GustaEagle/TCC_Calculadora_Acessivel/cronograma/cronograma.md

# Cronograma do projeto (calculadora — TCC)

Documento de referência temporal: organização **semana a semana**, com base no consolidado que você já tinha (intervalos e marcos com data única).  
Não substitui PRD, casos de uso, requisitos nem demais artefatos de engenharia de software — serve só como **linha do tempo** para alinhar entregas físicas, texto do trabalho e material de apresentação.

---

## Como ler este cronograma

- **Semanas:** domingo a sábado, numeradas a partir de **01/03/2026** (domingo).
- **“Em vigência”:** intervalos do plano original que **cruzam** aquela semana (podem continuar nas semanas seguintes).
- **“Marcos (data única)”:** acontecimentos previstos para um dia específico no consolidado.
- **Última data do consolidado:** **25/09/2026** (término previsto da criação do banner). Ajuste o fechamento com a data real da banca ou do curso, se for anterior.

---

## Visão geral do horizonte

| Marco global | Data |
| --- | --- |
| Início do consolidado | 01/03/2026 |
| Última data registrada | 25/09/2026 |

---

## Datas importantes (equipe / instituição)

Estas datas **complementam** o export bruto em [`cronograma_raw.txt`](cronograma_raw.txt) e deixam explícitos compromissos já combinados com orientação.

| Data | Significado |
| ---- | --- |
| **24/05/2026** | **Parte escrita homologada** com o professor **Yuri**: introdução; materiais e métodos; resultados e discussão; **esboço** de conclusão (texto praticamente aceito nesse conjunto). |
| **10/06/2026** | **Entrega da parte física + software**: produto integrado (hardware encapsulado + software embarcado) alinhado ao marco de **encapsulamento finalizado** do plano. |

---

## Cronograma semanal

### Março de 2026

#### Semana 1 — 01/03 a 07/03/2026

**Em vigência:** fabricação do teclado; teste no monitor; encapsulamento; testes aritméticos.

#### Semana 2 — 08/03 a 14/03/2026

**Em vigência:** fabricação do teclado; teste no monitor; encapsulamento; testes aritméticos.

#### Semana 3 — 15/03 a 21/03/2026

**Em vigência:** fabricação do teclado; teste no monitor; encapsulamento; testes aritméticos; agendamento de reunião (até 01/04/2026).

#### Semana 4 — 22/03 a 28/03/2026

**Em vigência:** fabricação do teclado; teste no monitor; encapsulamento; testes aritméticos; agendamento de reunião (até 01/04/2026).

#### Semana 5 — 29/03 a 04/04/2026

**Em vigência:** fabricação do teclado; teste no monitor; encapsulamento; testes aritméticos; agendamento de reunião (até 01/04/2026).

---

### Abril de 2026

#### Semana 6 — 05/04 a 11/04/2026

**Em vigência:** fabricação do teclado; teste no monitor; encapsulamento; testes aritméticos; **materiais e métodos (texto do TCC, 02/04 a 21/04)**; resultados e discussões (texto do TCC, a partir de 10/04).

#### Semana 7 — 12/04 a 18/04/2026

**Em vigência:** fabricação do teclado; teste no monitor; encapsulamento; testes aritméticos; **materiais e métodos (texto do TCC, até 21/04)**; resultados e discussões (texto do TCC); introdução (texto do TCC, a partir de 13/04).

#### Semana 8 — 19/04 a 25/04/2026

**Em vigência:** fabricação do teclado; encapsulamento; testes aritméticos; **materiais e métodos (texto do TCC, até 21/04)**; resultados e discussões (texto do TCC); introdução (texto do TCC); desenvolvimento (texto do TCC, a partir de 23/04).  
**Observação:** o intervalo de **teste no monitor** encerra em **15/04/2026** (semana anterior), logo ele não aparece mais a partir desta semana.  
**Marcos (export bruto):** fabricação PCB **07/04**; teste de PCB **14/04**; partes visuais **15/04**; revisão documentação **20/04**; refabricação e ajustes **24/04**; aquisição da bateria **25/04** (ver tabela de referência).

#### Semana 9 — 26/04 a 02/05/2026

**Em vigência:** fabricação do teclado; encapsulamento; testes aritméticos; resultados e discussões (texto do TCC); introdução (texto do TCC); desenvolvimento (texto do TCC).  
**Marcos (data única):** testes PCB 02 em **01/05/2026**.

---

### Maio de 2026

#### Semana 10 — 03/05 a 09/05/2026

**Em vigência:** encapsulamento; testes aritméticos; resultados e discussões (texto do TCC); introdução (texto do TCC); desenvolvimento (texto do TCC); resultados (texto do TCC, a partir de 05/05).  
**Marcos (data única):** revisão introdução (professor) em **04/05/2026**.

#### Semana 11 — 10/05 a 16/05/2026

**Em vigência:** encapsulamento; resultados e discussões (texto do TCC); desenvolvimento (texto do TCC); resultados (texto do TCC); conclusão (texto do TCC, a partir de 15/05); criação de banner (a partir de 15/05).  
**Marcos (data única):** revisão de documentação em **10/05/2026**; revisão materiais e métodos em **14/05/2026**; testes logarítmicos em **15/05/2026**.

#### Semana 12 — 17/05 a 23/05/2026

**Em vigência:** encapsulamento; resultados e discussões (texto do TCC); resultados (texto do TCC); conclusão (texto do TCC); criação de banner.  
**Marcos (data única):** revisão resultados e discussão (professor) em **18/05/2026**; outras funções (testes) em **22/05/2026**; revisão conclusão e revisão final em **23/05/2026**.

#### Semana 13 — 24/05 a 30/05/2026

**Em vigência:** encapsulamento; conclusão (texto do TCC); criação de banner.  
**Marcos (equipe):** **24/05/2026** — parte escrita homologada com o **prof. Yuri** (introdução; materiais e métodos; resultados e discussão; esboço de conclusão). Ver secção [Datas importantes](#datas-importantes-equipe--instituição).

---

### Junho de 2026

#### Semana 14 — 31/05 a 06/06/2026

**Em vigência:** encapsulamento; criação de banner.

#### Semana 15 — 07/06 a 13/06/2026

**Em vigência:** encapsulamento; criação de banner.  
**Marcos (data única):** **10/06/2026** — **encapsulamento finalizado** no consolidado; na prática da equipe, **entrega da parte física + software** (produto integrado). Ver secção [Datas importantes](#datas-importantes-equipe--instituição).

#### Semana 16 — 14/06 a 20/06/2026

**Em vigência:** criação de banner (até **25/09/2026**).

---

### Julho a setembro de 2026

Do **21/06/2026** em diante, o consolidado não traz novos intervalos além da **criação de banner**, com término previsto em **25/09/2026**. As semanas abaixo documentam esse período de forma explícita, sem inventar entregas intermediárias.

#### Semana 17 — 21/06 a 27/06/2026

**Em vigência:** criação de banner (até 25/09/2026).

#### Semana 18 — 28/06 a 04/07/2026

**Em vigência:** criação de banner (até 25/09/2026).

#### Semana 19 — 05/07 a 11/07/2026

**Em vigência:** criação de banner (até 25/09/2026).

#### Semana 20 — 12/07 a 18/07/2026

**Em vigência:** criação de banner (até 25/09/2026).

#### Semana 21 — 19/07 a 25/07/2026

**Em vigência:** criação de banner (até 25/09/2026).

#### Semana 22 — 26/07 a 01/08/2026

**Em vigência:** criação de banner (até 25/09/2026).

#### Semana 23 — 02/08 a 08/08/2026

**Em vigência:** criação de banner (até 25/09/2026).

#### Semana 24 — 09/08 a 15/08/2026

**Em vigência:** criação de banner (até 25/09/2026).

#### Semana 25 — 16/08 a 22/08/2026

**Em vigência:** criação de banner (até 25/09/2026).

#### Semana 26 — 23/08 a 29/08/2026

**Em vigência:** criação de banner (até 25/09/2026).

#### Semana 27 — 30/08 a 05/09/2026

**Em vigência:** criação de banner (até 25/09/2026).

#### Semana 28 — 06/09 a 12/09/2026

**Em vigência:** criação de banner (até 25/09/2026).

#### Semana 29 — 13/09 a 19/09/2026

**Em vigência:** criação de banner (até 25/09/2026).

#### Semana 30 — 20/09 a 26/09/2026

**Em vigência:** criação de banner (até **25/09/2026** — último dia previsto no consolidado).

---

## Referência: intervalos e datas do consolidado original

Tabela de conferência alinhada ao export [`cronograma_raw.txt`](cronograma_raw.txt) (Google Calendar), mais as **datas importantes** da equipe.  
_Notas:_ no raw aparece um evento “Encapsulamento finalizado” em **25/04** junto de “Aquisição da bateria”; isso **conflita** com o intervalo de encapsulamento até **10/06**. Aqui mantém-se **10/06** como encerramento do encapsulamento; **25/04** figura só como aquisição da bateria.

| Período / data | Descrição |
| --- | --- |
| 01/03/2026 a 01/05/2026 | Fabricação do teclado |
| 01/03/2026 a 15/04/2026 | Teste no monitor |
| 01/03/2026 a 10/06/2026 | Encapsulamento |
| 01/03/2026 a 04/05/2026 | Testes aritméticos |
| 18/03/2026 a 01/04/2026 | Agendar reunião |
| 02/04/2026 a 21/04/2026 | Materiais e métodos (texto TCC) |
| 10/04/2026 a 18/05/2026 | Resultados e discussões (texto TCC) |
| 13/04/2026 a 03/05/2026 | Introdução (texto TCC) |
| 23/04/2026 a 13/05/2026 | Desenvolvimento (texto TCC) |
| 05/05/2026 a 22/05/2026 | Resultados (texto TCC) |
| 15/05/2026 a 30/05/2026 | Conclusão (texto TCC) |
| 15/05/2026 a 25/09/2026 | Criação de banner |
| 02/04/2026 | Revisão documentação (dia inteiro) |
| 07/04/2026 | Fabricação PCB |
| 10/04/2026 | Revisão documentação; início resultados e discussões (texto) |
| 14/04/2026 | Teste de PCB |
| 15/04/2026 | Partes visuais |
| 20/04/2026 | Revisão documentação |
| 24/04/2026 | Refabricação e ajustes |
| 25/04/2026 | Aquisição da bateria |
| 30/04/2026 | Testes trigonométricos; revisão documentação |
| 01/05/2026 | Testes PCB 02 |
| 04/05/2026 | Revisão introdução (professor) |
| 10/05/2026 | Revisão de documentação |
| 14/05/2026 | Revisão materiais e métodos |
| 15/05/2026 | Testes logarítmicos |
| 18/05/2026 | Revisão resultados e discussão (professor) |
| 22/05/2026 | Outras funções (testes) |
| 23/05/2026 | Revisão conclusão e revisão final |
| **24/05/2026** | **Parte escrita homologada (prof. Yuri)** — introdução; materiais e métodos; resultados e discussão; esboço de conclusão |
| **10/06/2026** | **Encapsulamento finalizado** (consolidado); **entrega parte física + software** (equipe) |

---

## Observações finais

- O detalhamento de **PRD**, **casos de uso**, **requisitos** e demais documentos de software fica fora deste arquivo, conforme seu planejamento acadêmico.
- O ficheiro **bruto** [`cronograma_raw.txt`](cronograma_raw.txt) pode conter redundâncias do export; esta `cronograma.md` é a versão **curada** para o repositório.
- Se a banca ou o calendário da instituição fixar uma data de entrega **antes** de setembro, basta **recortar** o bloco final (banner e semanas correspondentes) para refletir a realidade da disciplina.
