GustaEagle/TCC_Calculadora_Acessivel/docs/desenvolvimento/Sprints.md

# Sprints e backlog (TCC Calculadora)

Fonte operacional de **execução** em paralelo ao [`PRD.md`](../produto/PRD.md) e ao [`cronograma/cronograma.md`](../../cronograma/cronograma.md).  
Equipe: **Gustavo**, **João**, **Yuri**.

---

## Como usar

- Cada **task** tem: ID, título, responsável sugerido, status.
- Status permitidos: `todo` | `doing` | `blocked` | `done`.
- Ao concluir: marcar `Status: done` e data curta no rodapé da task (opcional).
- **Não mover** tasks entre sprints sem acordo da equipe; prefira nova task na sprint corrente se for retrabalho.
- Alinhar entregáveis formais (professor) com o [`cronograma/cronograma.md`](../../cronograma/cronograma.md).
- A versão que **toda a equipe** deve assumir como referência é a de **`main` no GitHub** após **merge** do PR; editem nas branches de trabalho e integrem com frequência (ver [`GITHUB_WORKFLOW.md`](GITHUB_WORKFLOW.md), secção 3).

---

## Sprint 1 — Bootstrap repositório e documentação

### T1.1 — Padronizar fluxo Git e prompts de sessão

- **Responsável:** Gustavo (ou rotação)
- **Status:** done

### T1.2 — Manter `Sprints.md` e `CONTEXT.md` atualizados a cada sessão

- **Responsável:** todos
- **Status:** todo

### T1.3 — Definir convenção de branches e revisão de PR (equipe)

- **Responsável:** todos
- **Status:** todo

### T1.5 — Implementar logaritmo com base variável (Shift + log)

- **Responsável:** todos
- **Status:** done
- **Concluído em:** 2026-05-15

### T1.6 — Mudar botão "," para "." e adicionar comportamento SHIFT

- **Responsável:** todos
- **Status:** done
- **Concluído em:** 2026-05-16

### T1.4 — Criar arquivo de Materiais e métodos listando componentes

- **Responsável:** todos
- **Status:** done

---

## Sprint 2 — Refinamento de UI e Acessibilidade

### T2.1 — Botão de alternância de controles (Toggle keypad) no LCD

- **Responsável:** Yuri (ou rotação)
- **Status:** done
- **Concluído em:** 2026-06-10

### T2.2 — Corrigir visor para acompanhar expressões longas (Auto-scroll)

- **Responsável:** João (ou rotação)
- **Status:** done
- **Concluído em:** 2026-06-10

### T2.3 — Aumentar tamanho do visor para melhor legibilidade

- **Responsável:** Gustavo (ou rotação)
- **Status:** done
- **Concluído em:** 2026-06-10

### T2.4 — Aumentar fonte dos botões do teclado para acessibilidade

- **Responsável:** Yuri (ou rotação)
- **Status:** done
- **Concluído em:** 2026-06-10

### T2.5 — Ampliar fontes de resultados (Display, Rodapé, Histórico)

- **Responsável:** João (ou rotação)
- **Status:** done
- **Concluído em:** 2026-06-10

### T2.6 — Maximizar tamanho do visor de resultados (Ultra-size)

- **Responsável:** Gustavo (ou rotação)
- **Status:** done
- **Concluído em:** 2026-06-10

### Task T2.7 — Ajustar layout para garantir expansão visual do visor

- **Responsável:** Yuri (ou rotação)
- **Status:** done
- **Concluído em:** 2026-06-10

### Task T2.8 — Reverter display para Label (com fontes gigantes) e suporte a truncagem

- **Status:** done
- **Concluído em:** 2026-06-10

### Task T2.9 — Implementar layout responsivo (Scaling automático)

- **Responsável:** Yuri (ou rotação)
- **Status:** done
- **Concluído em:** 2026-06-10

### Task T2.10 — Polimento final: Silenciar toggle e expandir limites do visor

- **Responsável:** Gustavo (ou rotação)
- **Status:** done
- **Concluído em:** 2026-06-10

---

## Histórico rápido de alterações

| Data | Nota |
| ---- | ---- |
| 2026-04-18 | Criação do arquivo e Sprint 1 inicial. |
