GustaEagle/TCC_Calculadora_Acessivel/docs/produto/PRD.md

# Documento de requisitos de produto (PRD)

**Projeto:** calculadora científica acessível (hardware + software embarcado)  
**Versão do documento:** 1.5
**Status:** rascunho iterativo — evoluir junto ao TCC e à implementação  
**Referências:** `TCC.txt` (texto legado de materiais/métodos e escopo de funções); `prompt-prd-raspberry.md` (briefing original, não versionado); planejamento temporal em [cronograma/cronograma.md](../../cronograma/cronograma.md); fluxo Git e equipe em [desenvolvimento/GITHUB_WORKFLOW.md](../desenvolvimento/GITHUB_WORKFLOW.md); backlog operacional em [desenvolvimento/Sprints.md](../desenvolvimento/Sprints.md); memória de sessão em [desenvolvimento/CONTEXT.md](../desenvolvimento/CONTEXT.md); índice de documentação em [docs/README.md](../README.md); mapa de pastas do repositório em [desenvolvimento/REPO_STRUCTURE.md](../desenvolvimento/REPO_STRUCTURE.md); Waveshare (notas + CAD) em [waveshare/README.md](../waveshare/README.md); GPIO do Pi 4 em [raspberry-pi-4b/README.md](../raspberry-pi-4b/README.md).

---

## 1. Resumo executivo

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

---

## 2. Relação com o material legado (`TCC.txt`)

O arquivo `TCC.txt` acompanha o trabalho acadêmico (incluindo **materiais, métodos** e o **catálogo de funções** da seção 2.5), mas **não descreve mais a arquitetura vigente** do produto. Este PRD trata apenas da calculadora baseada em **Raspberry Pi 4B**, **periféricos Waveshare** (UPS HAT + LCD 4,3"), **segunda saída HDMI** para monitor, **switches hotswap**, **PCI em fenolite dupla face 15×15 cm** (KiCad + percloreto de ferro) e do **comportamento de software** previsto aqui. A redação formal do TCC (normas, figuras, metodologia) evolui em paralelo.

---

## 3. Objetivos e modos de uso

### 3.1 Objetivos

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

### Modos de uso (visão do produto)

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

---

## 4. Personas e casos de uso (resumo)

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

---

## 5. Escopo matemático (catálogo de funções)

Conforme a seção **2.5 — Recursos disponíveis** de `TCC.txt`, o produto deve suportar pelo menos:

### Funções trigonométricas

- **Seno** (`sen`)
  - **Arco-seno** (`sen⁻¹`)

- **Cosseno** (`cos`)
  - **Arco-cosseno** (`cos⁻¹`)

- **Tangente** (`tan`)
  - **Arco-tangente** (`tan⁻¹`)

---

### Funções logarítmicas

- **Logaritmo decimal** (`log`)
  - **Logaritmo natural** (`ln`)

---

### Constantes matemáticas

- Constante de Euler (`e`)
- Constante pi (`π`)

---

### Operações algébricas

- Exponenciação (`xʸ` ou `^`)
- Raiz quadrada (`√`)
- Inversão de valor (`x⁻¹`)
- Fatorial (`x!`)

---

### Operações combinatórias

- **Combinação** (`nCr`)
  - **Permutação** (`nPr`)

---

### Conversões de coordenadas

- Conversão coordenada **polar → retangular**
  - Conversão coordenada **retangular → polar**

---

### Controle e manipulação de entrada

- Operador deletar (`DEL`)
- Limpar / retornar ao valor anterior (`AC`)
- Resposta anterior (`Ans`)

---

### Estrutura de expressão

- Parênteses de agrupamento:
  - `(`
  - `)`

- Separadores numéricos:
  - Vírgula (`,`)
  - Ponto decimal (`.`)

---

### Operações aritméticas básicas

- Soma (`+`)
- Subtração (`−`)
- Multiplicação (`×`)
- Divisão (`÷`)

---

**Requisito:** a **lógica de cálculo** do sistema deve produzir resultados **consistentes** com esse catálogo; regras de precedência, formato numérico e tratamento de erros seguem a **seção 13** (códigos e feedback). Definições formais de cada função (domínio no plano real, convenções de ângulo graus/radianos se aplicável) permanecem **alinhadas ao texto acadêmico** em `TCC.txt` §2.5 — não é necessário repetir no PRD uma especificação matemática longa, desde que o comportamento implementado seja o mesmo.

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

---

## 6. Arquitetura de hardware (alto nível)

| Componente | Papel |
| --- | ----- |
| Raspberry Pi 4B | SBC principal: SO, aplicação, áudio, vídeo. |
| Waveshare UPS HAT | Continuidade elétrica; leitura de carga por **I2C** (ver [waveshare/UPS_HAT.md](../waveshare/UPS_HAT.md)); **avisos** (ex.: **TTS** com bateria baixa) quando implementado; **sem** exigência de persistência de sessão após encerramento. |
| LCD Waveshare **4,3" HDMI (B)** | Painel local; **modelo, cablagem e `config.txt`** em [waveshare/4.3inch_HDMI_LCD_B.md](../waveshare/4.3inch_HDMI_LCD_B.md). **Interruptor físico** no encapsulamento (com **Braille** no exterior) desliga a **saída HDMI** para o LCD; o painel entra em **standby** conforme o circuito. |
| Monitor HDMI externo | Segunda saída HDMI; quando em uso, torna-se a saída visual principal com **front dedicado**. |
| Teclado físico | **Cherry MX Red** em **hotswap**; trilhas na **fenolite**; **barra de pinos** + **cabo flat** até aos **GPIO** do Pi para matriz **6×7**. **Lista de GPIOs e funções** por documento de hardware (a acrescentar). |
| Identificação **Braille** | Peças em **PLA** (impressão **Bambu Lab A1**); notação **Braille português (BR)** segundo **normas oficiais** (rótulos no interruptor / teclas conforme desenho). |
| PCI | **Fenolite**, **dupla face**, **15×15 cm**; esquemático e layout no **KiCad**; produção por corrosão com **percloreto de ferro**. |

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

---

## 7. Saída de vídeo e áudio (requisitos centrais)

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

### 7.0 Interruptor físico do LCD

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

### 7.1 Apenas o HDMI do LCD reconhecido

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

### 7.2 HDMI do LCD e HDMI do monitor reconhecidos ao mesmo tempo

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

### 7.3 Áudio em paralelo (sempre)

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

### 7.4 Fluxo lógico (referência)

```mermaid
flowchart TD
  start[Inicio]
  both{LCD_e_monitor_HDMI_reconhecidos}
  start --> both
  both -->|"sim"| uiHdmi[Front_apenas_no_monitor]
  both -->|"nao"| lcdOnly{LCD_HDMI_reconhecido}
  lcdOnly -->|"sim"| uiLcd[Front_no_LCD]
  lcdOnly -->|"nao"| noVideo[Sem_video_utilizavel]
  uiHdmi --> audio[Audio_paralelo_sempre]
  uiLcd --> audio
  noVideo --> audio
```

---

## 8. Software (alto nível)

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

**Organização de código:** mantém-se a ideia de módulos separados (equivalente conceitual a `core`, interfaces e `accessibility` citados em `TCC.txt`, seção 2.6), **sem** amarrar o PRD a frameworks legados do texto acadêmico.

---

## 9. Requisitos funcionais

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

---

## 10. Requisitos não funcionais

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

---

## 11. Riscos e dependências

- **Hotplug HDMI no Linux:** eventos de conexão e nomes de saídas (`HDMI-A-1`, `HDMI-A-2`) variam conforme kernel/driver; pode exigir `udev`, `libdrm` ou camadas do compositor. Como o papel de cada painel vem da **porta física** (§6: HDMI0 = LCD, HDMI1 = monitor), é a **correspondência porta ↔ nome de conector** que precisa de ser verificada no hardware; trocar os cabos de porta inverte os fronts.
- **Driver e modo do LCD Waveshare:** seguir [waveshare/4.3inch_HDMI_LCD_B.md](../waveshare/4.3inch_HDMI_LCD_B.md); alterações de SO podem exigir revisão de `config.txt` / firmware.
- **Sincronização UI + áudio:** evitar anúncios duplicados ou fora de ordem ao trocar de modo.
- **Fabricação em fenolite:** tolerâncias e corrosão caseira afetam confiabilidade da PCI; revisão de largura de trilha/isolamento no KiCad.
- **Bateria e UPS:** autonomia limitada; **avisos** por TTS conforme RF-06; **sem** política de backup de sessão na baseline.

---

## 12. Itens em aberto / perguntas ao autor

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

**Decisões já registadas (não reabrir aqui):** modelo LCD **4,3" HDMI (B)** Waveshare em `docs/waveshare/`; **interruptor físico** do LCD com **Braille** no encapsulamento; **Braille PT-BR** em **PLA** (Bambu Lab A1); teclado **Cherry MX Red** + **hotswap** + **flat** para GPIO **sem** MCU intermédio; **HDMI0 = LCD** e **HDMI1 = monitor externo**; **motor de cálculo em Python**; **TTS em português (Brasil)** pela voz neural **`cadu` (Piper)**, offline, com o **`espeak-ng`** como fonemizador e **fallback** (WRN-011); UPS com **aviso de carga**, **sem** persistência obrigatória de sessão.

---

## 13. Erros, códigos e feedback (visual + TTS)

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

### 13.1 Convenções gerais

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

### 13.2 Tabela de erros e avisos (baseline)

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

### 13.3 Extensão da tabela

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

---

## 14. Histórico de revisões

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
