GustaEagle/TCC_Calculadora_Acessivel/docs/desenvolvimento/sessoes/semana-12.md

# Registro semanal — Semana 12 do plano

**Intervalo (domingo a sábado):** 17/05/2026 a 23/05/2026

_Registar abaixo todas as sessões da semana. Ordem: mais antigo no topo de cada secção, mais recente em baixo._

---

## Gustavo

_(nenhuma sessão registada)_

---

## João

- **Data:** 2026-05-17
- **Task / ID:** Validação Aritmética / T1.2
- **Feito:**
  - Bootstrap completo da sessão.
  - Implementação de suporte a porcentagem (`%`) no engine de cálculo.
  - Criação de suíte de testes unitários (`test_arithmetic.py`) com 15 casos de alta performance e robustez.
  - Correção de bugs de normalização (maiúsculas em funções, símbolos UTF-8).
  - Validação de identidades matemáticas, associatividade e precisão (epsilon).

---

## Yuri

_(nenhuma sessão registada)_

---

## Notas da equipa (opcional)

- Próximo passo é discutir os resultados dos testes com o professor Yuri em 18/05/2026.
