GustaEagle/TCC_Calculadora_Acessivel/docs/desenvolvimento/sessoes/semana-11.md

# Registro semanal — Semana 11 do plano

**Intervalo (domingo a sábado):** 10/05/2026 a 16/05/2026

---

## Gustavo

- 2026-05-15
- **Task / ID:** T1.5 — Implementar logaritmo com base variável (Shift + log)
- **Feito:** 
  - Implementação da função `logbase(base, value)` no motor de cálculo (`engine.py`).
  - Adição de suporte ao estado `Shift` no `app.py` para disparar `logbase(`.
  - Inversão da ordem dos argumentos (base primeiro, valor depois) conforme feedback em tempo real.
  - Atualização do dicionário de vozes para feedback acessível.
  - Testes unitários realizados com sucesso (7 testes passando).

---

## João

- 2026-05-14
- **Task / ID:** Fix Audio Feedback Interrupts
- **Feito:**
  - Modificação do `SpeechService` para suportar interrupção de áudio.
  - Integração do trigger de interrupção no `app.py` ao pressionar teclas.

---

## Yuri

_(nenhuma sessão registada)_

---

## Notas da equipa (opcional)

- Marco de "Testes logarítmicos" atingido em 15/05/2026.
