GustaEagle/TCC_Calculadora_Acessivel/docs/desenvolvimento/sessoes/semana-07.md

# Registro semanal — Semana **7** do plano

**Intervalo (domingo a sábado):** 12/04/2026 a 18/04/2026

---

## Gustavo

_(sessões desta semana)_

---

## João

_(sessões desta semana)_

**2026-04-18**
- **Task:** T1.4 (Materiais e Métodos)
- **Feito:** Extração das informações dos componentes do projeto descritos nas orientações e documentação de todos os detalhes em `materiais_e_metodos_tcc.md`. `Sprints.md` e repositório remoto também sincronizados através de push da sessão.
- **Próximo passo:** Padronizar as issues de PR/Review (T1.3).

---

## Yuri

_(sessões desta semana)_

---

## Notas da equipa (opcional)

- Ficheiro criado para padronização do registo; preencher conforme forem trabalhando.
