GustaEagle/TCC_Calculadora_Acessivel/docs/desenvolvimento/sessoes/_template-semana.md

# Registro semanal — Semana **NN** do plano

**Intervalo (domingo a sábado):** _DD/MM/AAAA a DD/MM/AAAA_

_Registar abaixo todas as sessões da semana. Ordem: mais antigo no topo de cada secção, mais recente em baixo (ou o contrário, desde que a equipa seja consistente)._

---

## Gustavo

_(nenhuma sessão registada)_

---

## João

_(nenhuma sessão registada)_

---

## Yuri

_(nenhuma sessão registada)_

---

## Notas da equipa (opcional)

- Reuniões, decisões conjuntas, dependências entre pessoas.
