GustaEagle/TCC_Calculadora_Acessivel/docs/cad/raspberry-pi-4-model-b/Microphone Plug, RPi4ModelB.SLDPRT

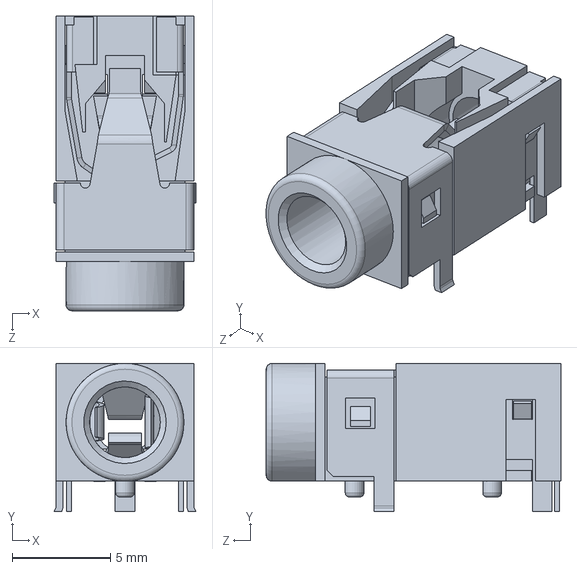
[picture p13: CAD file, 2026-04-18]
docs/cad/raspberry-pi-4-model-b/Microphone Plug, RPi4ModelB.SLDPRT
7.23 x 7.55 x 15.0 mm
