GustaEagle/TCC_Calculadora_Acessivel/docs/cad/raspberry-pi-4-model-b/VIA VL805 PCIe USB 3.0 controller, RPi4ModelB.SLDPRT

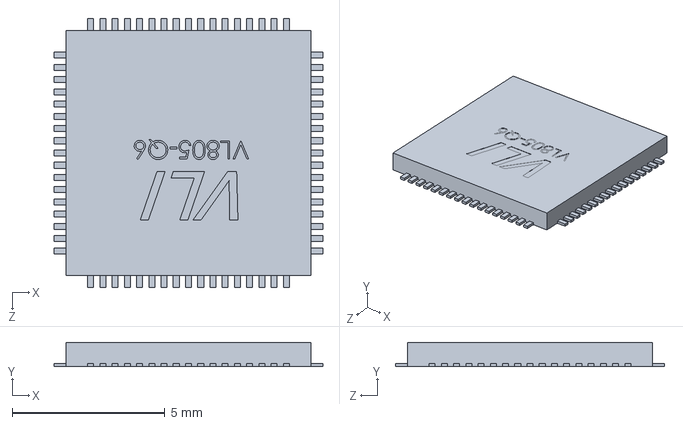
[picture p14: CAD file, 2026-04-18]
docs/cad/raspberry-pi-4-model-b/VIA VL805 PCIe USB 3.0 controller, RPi4ModelB.SLDPRT
8.80 x 0.8 x 8.80 mm
