GustaEagle/TCC_Calculadora_Acessivel/openspec/changes/archive/2026-09-10-add-hdmi-adaptive-layout/tasks.md

## 1. Regra de layout como módulo puro

- [x] 1.1 Criar `software/ui/shared/layout.py` com as constantes nomeadas: `REFERENCE_WIDTH/HEIGHT` (1280x720), `KEYPAD_MIN_WIDTH/HEIGHT` (900x600), `HISTORY_MIN_WIDTH/HEIGHT` (1200x700), `SCALE_FLOOR` (0.75) e `SCALE_CEILING` (2.0), com comentário explicando a origem de cada limiar (design D3).
- [x] 1.2 Definir `LayoutTier` (`COMPACT` / `MEDIUM` / `FULL`) e `tier_for(width, height)`, exigindo que **ambas** as dimensões atinjam o limiar (design D3).
- [x] 1.3 Implementar `scale_for(width, height)` = `clamp(min(w/REF_W, h/REF_H), SCALE_FLOOR, SCALE_CEILING)` (design D4).
- [x] 1.4 Implementar `font_sizes(scale)` a partir da tabela base atual e `display_limits(width, scale)`, com fator `(width/REF_W)/scale` — a largura é necessária: só a escala erraria no 4K (janela 3x maior, fonte no teto de 2x).
- [x] 1.5 Garantir que o módulo **não importa Tk/ttkbootstrap** (é o que o torna testável sem display).

## 2. Testes da regra (sem abrir janela)

- [x] 2.1 Criar `software/tests/test_hdmi_layout_tiers.py` cobrindo as três faixas, incluindo os **limites exatos** (ex.: 900x600 é média; 899x600 e 900x599 são compacta).
- [x] 2.2 Testar que uma tela larga e baixa (ex.: 1920x480) **não** ganha teclado — a regra é por eixo, não por área.
- [x] 2.3 Testar piso e teto da escala (ex.: 640x480 → `SCALE_FLOOR`; 3840x2160 → `SCALE_CEILING`).
- [x] 2.4 **Teste de não-regressão:** em 1280x720 a escala é 1.0 e `font_sizes(1.0)` reproduz exatamente os valores de `FONT_SIZES` de hoje (34/58/17/13/14).
- [x] 2.5 Testar que `display_limits` reduz o número de caracteres quando a escala cresce.
- [x] 2.6 Confirmar que os novos testes passam **sem** `DISPLAY` (`env -u DISPLAY python3 -m unittest ...`).

## 3. Consumir a regra no front HDMI

- [x] 3.1 Em [software/ui/hdmi/app.py](../../../software/ui/hdmi/app.py), derivar `self.tier` e `self.scale` na construção, a partir de `winfo_screenwidth/height` (mesma fonte já usada por `_screen_geometry`).
- [x] 3.2 Substituir o `FONT_SIZES` fixo e as constantes `MAX_*_CHARS` pelos valores derivados da escala, mantendo `resizable(False, False)`.
- [x] 3.3 Em `_build_layout`, montar o painel de histórico **apenas** na faixa completa — sem criar o widget nas demais, e sem deixar peso de coluna reservado (design D5).
- [x] 3.4 Montar o teclado (`keypad_frame`, `left_frame`, `right_frame`, botões) **apenas** nas faixas média e completa.
- [x] 3.5 Omitir o botão de alternar teclado no rodapé quando não há teclado, e ajustar `_set_initial_focus` para um alvo que exista em qualquer faixa.
- [x] 3.6 Tornar `_apply_controls_visibility` e `_update_keypad_labels` tolerantes a `self.buttons` vazio e a `keypad_frame` inexistente (faixa compacta).
- [x] 3.7 Conferir que a construção do front na troca de saída (RF-09) relê a tela nova — nada de estado de layout em variável de módulo.

## 4. Testes do front (com display)

- [x] 4.1 Acrescentar a `software/tests/` um teste que constrói o front e verifica que, na faixa completa, existem teclado, histórico e botão de alternância — usando o padrão dos testes de GUI já existentes (rodam sob Xvfb no CI).
- [x] 4.2 Verificar que a suíte completa continua passando (`make check`) e que o total de testes headless não regride.

## 5. Validação no hardware (Raspberry Pi 4B + monitor)

- [ ] 5.1 No monitor do TCC, confirmar a faixa **completa**: display, teclado e histórico legíveis, sem sobreposição nem corte.
- [ ] 5.2 Confirmar que a escala tipográfica melhora a leitura em relação ao layout fixo anterior (público com visão parcial, PRD §4).
- [ ] 5.3 Se houver monitor menor disponível, confirmar as faixas **média** e **compacta**; senão, registrar que ficaram cobertas apenas por teste unitário.
- [ ] 5.4 Confirmar que, na faixa compacta, a calculadora continua **totalmente operável pelo teclado físico** (RF-05) e que os anúncios de voz não mudam.
- [ ] 5.5 Revisar os limiares (D3) com o que foi observado e ajustar as constantes se o histórico ou o teclado ficarem apertados.

## 7. Medir a tela certa quando o monitor entra depois do boot (D6)

- [x] 7.1 Adicionar `screen_size()` a `software/hw_platform/video_output.py`, lendo `Screen ... current WxH` do `xrandr --query`, com `None` quando não há X/xrandr ou a saída é inesperada.
- [x] 7.2 No front HDMI, ler a tela **uma vez** por `_active_screen_size()` (xrandr primeiro, Tk como fallback) e usar o mesmo valor para a geometria da janela e para faixa/escala.
- [x] 7.3 Registrar no log as duas medidas (a usada e a que o Tk reportava), para diagnosticar no kiosk sem terminal.
- [x] 7.4 Testar `screen_size()`: cabeçalho lido, ausência de X/xrandr, saída sem cabeçalho, erro e timeout.
- [x] 7.5 Testar no front que o valor do xrandr **vence** o do Tk, que um valor velho de 800x480 produziria a faixa compacta (a regressão), e que sem xrandr o Tk é usado.
- [x] 7.6 Atualizar `test_window_geometry` para a nova fonte (o contrato mudou de "pergunta ao Tk" para "mede a tela, xrandr primeiro").

## 8. Revisão da suíte de testes

- [x] 8.1 Corrigir `test_keypad_toggle`: o teste chamava-se "defaults to a hidden keypad" e a mensagem dizia "não inicia com o teclado oculto", mas a asserção exigia `controls_visible = True` (visível) desde que `121c030` a inverteu de `False` para `True` — nome, mensagem e docstring alinhados ao comportamento real.
- [x] 8.2 Corrigir os comentários do front que afirmavam o oposto do código ("teclado começa oculto" sobre uma linha que o deixa visível), incluindo o docstring de `_set_initial_focus`.
- [x] 8.3 Recuperar cobertura perdida com a remoção de `test_responsive_layout.py` (em `992af79`): **piso de legibilidade por papel** (PRD §4) e **hierarquia visual** resultado > expressão > botão, agora em `LEGIBILITY_FLOORS` e testadas.
- [x] 8.4 Conferir que nenhum teste referencia caminhos antigos (`ui_lcd`/`ui_hdmi`) ou constantes removidas do front.
- [x] 8.5 Conferir que `test_history_shortcut` (janela fixa, sem `<Configure>`) e `test_image_packages` (xrandr na imagem) continuam válidos após a mudança.

## 9. Detecção de hardware: não confundir um PC com um Pi

- [x] 9.1 `SysfsHdmiPortReader.available()` passa a exigir **ambos** os conectores configurados, em vez de qualquer um: o Pi 4B enumera as duas portas HDMI (mesmo sem cabo), um notebook tem só uma. Antes, a máquina de desenvolvimento usava o leitor real, não achava a segunda porta e a calculadora abria em **modo somente áudio, sem janela**.
- [x] 9.2 Atualizar `test_display_selector`: o caso "disponível assim que um conector existe" codificava a heurística fraca; vira "um conector sozinho não é um Pi" + "disponível quando os dois existem".
- [x] 9.3 Corrigir o docstring de `detect_port_reader`, que justificava a heurística com "CI não tem conectores HDMI" — premissa falsa para qualquer notebook com porta HDMI.

## 6. Documentação

- [x] 6.1 Atualizar o docstring de [software/ui/hdmi/app.py](../../../software/ui/hdmi/app.py): ele hoje afirma que as fontes são declaradas uma vez e fixas — passa a ser "derivadas da resolução na construção, sem recomposição em runtime".
- [x] 6.2 Registrar as três faixas e os limiares onde a equipe encontre (README do software ou `docs/`), para que ajustar um número não exija ler o front inteiro.
