GustaEagle/TCC_Calculadora_Acessivel/software/tests/test_video_output.py

"""xrandr glue: point X at the panel that should show the UI (RF-09).

Detecting the change is not enough - X keeps driving whatever it configured at
startup, so a monitor plugged in later stays dark until an output is enabled.
And enabling it is not enough either: the exit code says the command was
accepted, not that the panel actually changed, which is how both screens stayed
lit while the code reported success.
"""

import contextlib
import subprocess
import unittest
from unittest import mock

from software.hw_platform import video_output

# Real `xrandr --query` output from a Pi driving the LCD only: the monitor is
# plugged in but has no CRTC, which is the state the exclusivity has to produce.
QUERY_LCD_ONLY = """Screen 0: minimum 320 x 200, current 800 x 480, maximum 16384 x 16384
HDMI-1 connected primary 800x480+0+0 (normal left inverted right x axis y axis) 154mm x 86mm
   800x480       59.90*+
HDMI-2 connected (normal left inverted right x axis y axis) 598mm x 336mm
   1920x1080     60.00 +  50.00    59.94
"""

# The bug: X autoconfigured both panels side by side (an extended desktop).
QUERY_EXTENDED = """Screen 0: minimum 320 x 200, current 2720 x 1080, maximum 16384 x 16384
HDMI-1 connected primary 800x480+0+0 (normal left inverted right x axis y axis) 154mm x 86mm
   800x480       59.90*+
HDMI-2 connected 1920x1080+800+0 (normal left inverted right x axis y axis) 598mm x 336mm
   1920x1080     60.00*+  50.00
"""

QUERY_MONITOR_ONLY = """Screen 0: minimum 320 x 200, current 1920 x 1080, maximum 16384 x 16384
HDMI-1 connected (normal left inverted right x axis y axis) 154mm x 86mm
   800x480       59.90 +
HDMI-2 connected primary 1920x1080+0+0 (normal left inverted right x axis y axis) 598mm x 336mm
   1920x1080     60.00*+  50.00
"""


def fake_query(stdout: str):
    """A subprocess.run stand-in that answers `xrandr --query` with `stdout`."""
    return mock.Mock(returncode=0, stdout=stdout, stderr="")


# Rotacao que activate() ve' quando o teste nao esta' a falar de rotacao: os dois
# paineis como o xrandr os reporta por omissao, sem nenhuma volta aplicada.
UNROTATED = {"HDMI-1": "normal", "HDMI-2": "normal"}


@contextlib.contextmanager
def xrandr_ready(available: bool = True, rotations: dict[str, str] | None = UNROTATED):
    """Pin BOTH environment probes, so these tests do not depend on the machine
    running them actually having xrandr installed.

    Patching `available` alone is not enough: read_outputs() and activate()
    consult missing_xrandr_on_x() *first*. On a runner with a virtual display
    but no xrandr package that probe is True, so the call returns early and
    never reaches the patched `available` - every mocked-subprocess assertion
    then fails for a reason that has nothing to do with what is under test.
    The cases that deliberately exercise the missing-binary path patch
    shutil.which themselves and do not use this helper.

    `rotations` pins what activate() reads back as the panels' orientation, for
    the same reason the probes are pinned: a test about layout mocks
    subprocess.run with no usable stdout, so an unpinned rotation read would
    parse a Mock. `rotations=None` leaves the real reader in place, which is
    what the rotation tests themselves need.
    """
    patches = [
        mock.patch.object(video_output, "available", return_value=available),
        mock.patch.object(video_output, "missing_xrandr_on_x", return_value=False),
    ]
    if rotations is not None:
        patches.append(
            mock.patch.object(video_output, "read_rotations", return_value=rotations)
        )

    with contextlib.ExitStack() as stack:
        for patch in patches:
            stack.enter_context(patch)
        yield


class ReadOutputsTest(unittest.TestCase):
    """1.1/1.2: read the outputs X really has, and never raise doing it."""

    def read(self, stdout: str) -> dict[str, bool]:
        with xrandr_ready(True, rotations=None), \
             mock.patch("subprocess.run", return_value=fake_query(stdout)):
            return video_output.read_outputs()

    def test_parses_names_and_active_state(self) -> None:
        """Active means "has a CRTC", not merely "has a cable in"."""
        self.assertEqual(self.read(QUERY_LCD_ONLY), {"HDMI-1": True, "HDMI-2": False})

    def test_an_extended_desktop_shows_both_outputs_active(self) -> None:
        self.assertEqual(self.read(QUERY_EXTENDED), {"HDMI-1": True, "HDMI-2": True})

    def test_disconnected_outputs_are_listed_as_inactive(self) -> None:
        stdout = (
            "Screen 0: minimum 320 x 200, current 800 x 480, maximum 16384 x 16384\n"
            "HDMI-1 connected primary 800x480+0+0 (normal left inverted) 154mm x 86mm\n"
            "HDMI-2 disconnected (normal left inverted right x axis y axis)\n"
        )
        self.assertEqual(self.read(stdout), {"HDMI-1": True, "HDMI-2": False})

    def test_no_x_server_reads_as_unknown(self) -> None:
        with xrandr_ready(False), \
             mock.patch("subprocess.run") as run:
            self.assertEqual(video_output.read_outputs(), {})

        run.assert_not_called()

    def test_a_missing_xrandr_binary_reads_as_unknown(self) -> None:
        with xrandr_ready(True), \
             mock.patch("subprocess.run", side_effect=FileNotFoundError):
            self.assertEqual(video_output.read_outputs(), {})

    def test_a_hung_xrandr_reads_as_unknown(self) -> None:
        with xrandr_ready(True), \
             mock.patch("subprocess.run", side_effect=subprocess.TimeoutExpired("xrandr", 10)):
            self.assertEqual(video_output.read_outputs(), {})

    def test_a_failing_xrandr_reads_as_unknown(self) -> None:
        with xrandr_ready(True), \
             mock.patch("subprocess.run", side_effect=subprocess.CalledProcessError(1, "xrandr")):
            self.assertEqual(video_output.read_outputs(), {})

    def test_unexpected_output_format_reads_as_unknown(self) -> None:
        """A future xrandr that prints something else must not crash the boot."""
        self.assertEqual(self.read("uma saida completamente diferente\n"), {})


class NameMappingTest(unittest.TestCase):
    def test_drm_names_become_xrandr_names(self) -> None:
        """sysfs says HDMI-A-1; the X modesetting driver says HDMI-1."""
        self.assertEqual(video_output.drm_to_xrandr("HDMI-A-1"), "HDMI-1")
        self.assertEqual(video_output.drm_to_xrandr("HDMI-A-2"), "HDMI-2")

    def test_an_env_var_overrides_the_convention(self) -> None:
        """Bring-up may find other names on this kernel/driver pair."""
        with mock.patch.dict("os.environ", {"CALC_LCD_XRANDR_OUTPUT": "HDMI1"}):
            self.assertEqual(
                video_output.output_name("HDMI-A-1", video_output.LCD_OUTPUT_ENV),
                "HDMI1",
            )

    def test_without_the_env_var_the_connector_is_converted(self) -> None:
        with mock.patch.dict("os.environ", {}, clear=True):
            self.assertEqual(
                video_output.output_name("HDMI-A-2", video_output.MONITOR_OUTPUT_ENV),
                "HDMI-2",
            )

    def test_the_env_var_wins_over_an_output_present_in_x(self) -> None:
        """Highest precedence, so bring-up can force a name without a rebuild."""
        with mock.patch.dict("os.environ", {"CALC_MONITOR_XRANDR_OUTPUT": "DSI-1"}):
            self.assertEqual(
                video_output.output_name(
                    "HDMI-A-2", video_output.MONITOR_OUTPUT_ENV, {"HDMI-2": False}
                ),
                "DSI-1",
            )

    def test_a_name_present_in_x_wins_over_the_convention(self) -> None:
        """The whole bug: this kernel spells it HDMI2, the convention guessed HDMI-2."""
        with mock.patch.dict("os.environ", {}, clear=True):
            self.assertEqual(
                video_output.output_name(
                    "HDMI-A-2", video_output.MONITOR_OUTPUT_ENV, {"HDMI1": True, "HDMI2": False}
                ),
                "HDMI2",
            )

    def test_matching_ignores_hyphens_and_case(self) -> None:
        for spelling in ("HDMI-A-2", "HDMI-2", "HDMI2", "hdmi-2"):
            with mock.patch.dict("os.environ", {}, clear=True):
                self.assertEqual(
                    video_output.output_name(
                        "HDMI-A-2", video_output.MONITOR_OUTPUT_ENV, {spelling: False}
                    ),
                    spelling,
                )

    def test_falls_back_to_the_convention_when_x_knows_no_such_port(self) -> None:
        with mock.patch.dict("os.environ", {}, clear=True):
            self.assertEqual(
                video_output.output_name(
                    "HDMI-A-2", video_output.MONITOR_OUTPUT_ENV, {"DP-1": True}
                ),
                "HDMI-2",
            )


class LayoutMatchesTest(unittest.TestCase):
    """2.1: comparing the state read from X against the layout we want."""

    def test_target_alone_active_is_a_match(self) -> None:
        self.assertIs(
            video_output.layout_matches("HDMI-2", ("HDMI-1",), {"HDMI-1": False, "HDMI-2": True}),
            True,
        )

    def test_an_extended_desktop_is_not_a_match(self) -> None:
        self.assertIs(
            video_output.layout_matches("HDMI-2", ("HDMI-1",), {"HDMI-1": True, "HDMI-2": True}),
            False,
        )

    def test_the_wrong_panel_being_the_active_one_is_not_a_match(self) -> None:
        self.assertIs(
            video_output.layout_matches("HDMI-2", ("HDMI-1",), {"HDMI-1": True, "HDMI-2": False}),
            False,
        )

    def test_an_unreadable_state_is_neither_a_match_nor_a_mismatch(self) -> None:
        """None, not False: not knowing is not the same as knowing it is wrong."""
        self.assertIsNone(video_output.layout_matches("HDMI-2", ("HDMI-1",), {}))

    def test_a_target_x_does_not_know_is_unreadable(self) -> None:
        self.assertIsNone(
            video_output.layout_matches("HDMI-9", ("HDMI-1",), {"HDMI-1": True})
        )


class ActivateTest(unittest.TestCase):
    def test_does_nothing_without_an_x_server(self) -> None:
        """A developer machine has no DISPLAY and needs none of this."""
        with xrandr_ready(False), \
             mock.patch("subprocess.run") as run:
            self.assertFalse(video_output.activate("HDMI-2"))

        run.assert_not_called()

    def test_enables_the_target_and_disables_the_other_in_one_call(self) -> None:
        """One xrandr call, so the server reconfigures once instead of blanking."""
        with xrandr_ready(True), \
             mock.patch.object(
                 video_output, "layout_matches", side_effect=[False, True]
             ), \
             mock.patch("subprocess.run") as run:
            self.assertTrue(
                video_output.activate("HDMI-2", disable=("HDMI-1", "HDMI-2"))
            )

        argv = run.call_args.args[0]
        self.assertEqual(
            argv[:7],
            ["xrandr", "--output", "HDMI-2", "--auto", "--primary", "--rotate", "normal"],
        )
        self.assertEqual(argv[7:], ["--output", "HDMI-1", "--off"])

    def test_the_target_is_never_switched_off_by_its_own_call(self) -> None:
        with xrandr_ready(True), \
             mock.patch.object(video_output, "layout_matches", side_effect=[False, True]), \
             mock.patch("subprocess.run") as run:
            video_output.activate("HDMI-1", disable=("HDMI-1", "HDMI-2"))

        argv = run.call_args.args[0]
        self.assertNotIn("--off", argv[:6])
        self.assertEqual(argv.count("--off"), 1)

    def test_a_failing_xrandr_is_reported_not_raised(self) -> None:
        """The UI must come up even if the outputs could not be reconfigured."""
        with xrandr_ready(True), \
             mock.patch.object(video_output, "layout_matches", return_value=False), \
             mock.patch("subprocess.run", side_effect=subprocess.CalledProcessError(1, "xrandr")):
            self.assertFalse(video_output.activate("HDMI-2"))

    def test_a_hung_xrandr_does_not_hang_the_app(self) -> None:
        with xrandr_ready(True), \
             mock.patch.object(video_output, "layout_matches", return_value=False), \
             mock.patch("subprocess.run", side_effect=subprocess.TimeoutExpired("xrandr", 10)):
            self.assertFalse(video_output.activate("HDMI-2"))

    def test_a_missing_xrandr_binary_is_not_fatal(self) -> None:
        with xrandr_ready(True), \
             mock.patch.object(video_output, "layout_matches", return_value=False), \
             mock.patch("subprocess.run", side_effect=FileNotFoundError):
            self.assertFalse(video_output.activate("HDMI-2"))


class ActivateIdempotenceTest(unittest.TestCase):
    """2.2: the boot-time call and the per-front call must not re-flash the screen."""

    def test_a_correct_layout_skips_xrandr_entirely(self) -> None:
        with xrandr_ready(True), \
             mock.patch.object(video_output, "read_outputs",
                               return_value={"HDMI-1": False, "HDMI-2": True}), \
             mock.patch("subprocess.run") as run:
            self.assertTrue(video_output.activate("HDMI-2", disable=("HDMI-1",)))

        run.assert_not_called()

    def test_an_extended_desktop_is_reconfigured(self) -> None:
        with xrandr_ready(True), \
             mock.patch.object(video_output, "read_outputs",
                               side_effect=[{"HDMI-1": True, "HDMI-2": True},
                                            {"HDMI-1": False, "HDMI-2": True}]), \
             mock.patch("subprocess.run") as run:
            self.assertTrue(video_output.activate("HDMI-2", disable=("HDMI-1",)))

        run.assert_called_once()


class ActivateVerificationTest(unittest.TestCase):
    """2.3/2.4: exit code 0 is not proof that the CRTC changed."""

    def test_a_confirmed_layout_is_reported_as_success(self) -> None:
        with xrandr_ready(True), \
             mock.patch.object(video_output, "read_outputs",
                               side_effect=[{"HDMI-1": True, "HDMI-2": True},
                                            {"HDMI-1": False, "HDMI-2": True}]), \
             mock.patch("subprocess.run"):
            self.assertTrue(video_output.activate("HDMI-2", disable=("HDMI-1",)))

    def test_xrandr_succeeding_while_the_lcd_stays_on_is_a_failure(self) -> None:
        """Exactly the observed bug: command accepted, both panels still lit."""
        with xrandr_ready(True), \
             mock.patch.object(video_output, "read_outputs",
                               side_effect=[{"HDMI-1": True, "HDMI-2": True},
                                            {"HDMI-1": True, "HDMI-2": True}]), \
             mock.patch("subprocess.run") as run:
            self.assertFalse(video_output.activate("HDMI-2", disable=("HDMI-1",)))

        run.assert_called_once()

    def test_an_unverifiable_state_is_reported_but_does_not_raise(self) -> None:
        """The front still has to start; only the return value says "unproven"."""
        with xrandr_ready(True), \
             mock.patch.object(video_output, "read_outputs", side_effect=[{}, {}]), \
             mock.patch("subprocess.run"):
            self.assertFalse(video_output.activate("HDMI-2", disable=("HDMI-1",)))


class MissingXrandrTest(unittest.TestCase):
    """The real bug on the Pi: the image never installed the xrandr client.

    `xorg-server` does not ship it - it is its own apk - so every call was a
    silent no-op at debug level and both panels stayed lit. Indistinguishable,
    in the log, from a developer machine with no X at all.
    """

    def test_an_x_server_without_xrandr_is_flagged(self) -> None:
        with mock.patch.dict("os.environ", {"DISPLAY": ":0"}), \
             mock.patch("shutil.which", return_value=None):
            self.assertTrue(video_output.missing_xrandr_on_x())

    def test_a_machine_without_x_is_not_flagged(self) -> None:
        """A developer PC is behaving correctly and must stay quiet."""
        with mock.patch.dict("os.environ", {}, clear=True), \
             mock.patch("shutil.which", return_value=None):
            self.assertFalse(video_output.missing_xrandr_on_x())

    def test_a_working_setup_is_not_flagged(self) -> None:
        with mock.patch.dict("os.environ", {"DISPLAY": ":0"}), \
             mock.patch("shutil.which", return_value="/usr/bin/xrandr"):
            self.assertFalse(video_output.missing_xrandr_on_x())

    def test_the_missing_binary_is_logged_as_wrn_012_not_debug(self) -> None:
        """One boot has to be enough to see this in ~/calculadora.log."""
        with mock.patch.dict("os.environ", {"DISPLAY": ":0"}), \
             mock.patch("shutil.which", return_value=None), \
             mock.patch("subprocess.run") as run, \
             self.assertLogs(video_output.logger, level="WARNING") as logs:
            self.assertFalse(
                video_output.activate("HDMI-2", disable=("HDMI-1",), mode="hdmi")
            )

        run.assert_not_called()
        recorded = "\n".join(logs.output)
        self.assertIn("WRN-012", recorded)
        self.assertIn("xrandr", recorded)

    def test_a_developer_machine_stays_silent(self) -> None:
        """No DISPLAY is not a fault; it must not cry wolf in the CI log."""
        with mock.patch.dict("os.environ", {}, clear=True), \
             mock.patch("shutil.which", return_value=None), \
             mock.patch("subprocess.run") as run:
            with self.assertRaises(AssertionError):
                with self.assertLogs(video_output.logger, level="WARNING"):
                    video_output.activate("HDMI-2", disable=("HDMI-1",))

        run.assert_not_called()


class LayoutLoggingTest(unittest.TestCase):
    """3.2: a bring-up with no console must still be able to see what happened."""

    def test_a_failure_logs_wrn_012_with_the_mode_and_the_names(self) -> None:
        with xrandr_ready(True), \
             mock.patch.object(video_output, "read_outputs",
                               side_effect=[{"HDMI-1": True, "HDMI-2": True},
                                            {"HDMI-1": True, "HDMI-2": True}]), \
             mock.patch("subprocess.run"), \
             self.assertLogs(video_output.logger, level="WARNING") as logs:
            video_output.activate("HDMI-2", disable=("HDMI-1",), mode="hdmi")

        recorded = "\n".join(logs.output)
        self.assertIn("WRN-012", recorded)
        self.assertIn("hdmi", recorded)
        self.assertIn("HDMI-2", recorded)
        self.assertIn("HDMI-1", recorded)

    def test_a_success_is_logged_with_the_mode_and_the_names(self) -> None:
        with xrandr_ready(True), \
             mock.patch.object(video_output, "read_outputs",
                               side_effect=[{"HDMI-1": True, "HDMI-2": True},
                                            {"HDMI-1": False, "HDMI-2": True}]), \
             mock.patch("subprocess.run"), \
             self.assertLogs(video_output.logger, level="INFO") as logs:
            video_output.activate("HDMI-2", disable=("HDMI-1",), mode="hdmi")

        recorded = "\n".join(logs.output)
        self.assertNotIn("WRN-012", recorded)
        self.assertIn("hdmi", recorded)
        self.assertIn("HDMI-2", recorded)


if __name__ == "__main__":
    unittest.main()


class ScreenSizeTest(unittest.TestCase):
    """O tamanho da tela vem do xrandr, nao do valor cacheado pelo Xlib.

    Regressao real: com o monitor ligado depois do boot (RF-09, o caso normal),
    o front HDMI subia no tamanho minimo. winfo_screenwidth() devolve a struct
    Screen que o Xlib preencheu ao abrir a conexao e NAO e' atualizada quando o
    RandR redimensiona a tela - entao o Tk ainda reportava os 800x480 do LCD.
    """

    def size(self, stdout: str):
        with xrandr_ready(True), \
             mock.patch("subprocess.run", return_value=fake_query(stdout)):
            return video_output.screen_size()

    def test_reads_the_current_screen_from_the_header(self) -> None:
        self.assertEqual(self.size(QUERY_MONITOR_ONLY), (1920, 1080))

    def test_reads_the_lcd_only_screen(self) -> None:
        self.assertEqual(self.size(QUERY_LCD_ONLY), (800, 480))

    def test_an_extended_desktop_reports_the_whole_screen(self) -> None:
        """Estado que a exclusividade tem de eliminar; ainda assim, sem crash."""
        self.assertEqual(self.size(QUERY_EXTENDED), (2720, 1080))

    def test_output_without_the_header_is_unknown(self) -> None:
        self.assertIsNone(self.size("HDMI-1 connected 800x480+0+0\n"))

    def test_no_x_or_no_xrandr_is_unknown(self) -> None:
        """Fora do Pi nao ha o que perguntar - quem chama cai no Tk."""
        with xrandr_ready(False):
            self.assertIsNone(video_output.screen_size())

    def test_a_failing_xrandr_is_unknown_not_an_exception(self) -> None:
        with xrandr_ready(True), \
             mock.patch("subprocess.run", side_effect=subprocess.CalledProcessError(1, "xrandr")):
            self.assertIsNone(video_output.screen_size())

    def test_a_timeout_is_unknown_not_an_exception(self) -> None:
        with xrandr_ready(True), \
             mock.patch("subprocess.run", side_effect=subprocess.TimeoutExpired("xrandr", 10)):
            self.assertIsNone(video_output.screen_size())


class AllOffTest(unittest.TestCase):
    """video-blackout 1.1-1.4: the user's command switches every panel off."""

    def test_both_panels_go_off_in_a_single_call(self) -> None:
        """1.1: one xrandr call, so the server reconfigures once."""
        with xrandr_ready(True), \
             mock.patch.object(video_output, "read_outputs",
                               side_effect=[{"HDMI-1": True, "HDMI-2": True},
                                            {"HDMI-1": False, "HDMI-2": False}]), \
             mock.patch("subprocess.run") as run:
            self.assertTrue(video_output.all_off(("HDMI-1", "HDMI-2")))

        run.assert_called_once()
        self.assertEqual(
            run.call_args.args[0],
            ["xrandr", "--output", "HDMI-1", "--off", "--output", "HDMI-2", "--off"],
        )

    def test_an_output_left_active_by_the_reread_is_a_failure(self) -> None:
        """1.2: accepted by xrandr is not the same as dark."""
        with xrandr_ready(True), \
             mock.patch.object(video_output, "read_outputs",
                               side_effect=[{"HDMI-1": True, "HDMI-2": False},
                                            {"HDMI-1": True, "HDMI-2": False}]), \
             mock.patch("subprocess.run"), \
             self.assertLogs(video_output.logger, level="WARNING") as logs:
            self.assertFalse(video_output.all_off(("HDMI-1", "HDMI-2"), mode="lcd"))

        recorded = "\n".join(logs.output)
        self.assertIn("WRN-013", recorded)
        self.assertIn("HDMI-1", recorded)

    def test_an_unreadable_reread_is_a_failure(self) -> None:
        with xrandr_ready(True), \
             mock.patch.object(video_output, "read_outputs",
                               side_effect=[{"HDMI-1": True}, {}]), \
             mock.patch("subprocess.run"), \
             self.assertLogs(video_output.logger, level="WARNING"):
            self.assertFalse(video_output.all_off(("HDMI-1", "HDMI-2")))

    def test_a_failing_xrandr_is_reported_not_raised(self) -> None:
        with xrandr_ready(True), \
             mock.patch.object(video_output, "read_outputs", return_value={"HDMI-1": True}), \
             mock.patch("subprocess.run", side_effect=subprocess.CalledProcessError(1, "xrandr")), \
             self.assertLogs(video_output.logger, level="WARNING"):
            self.assertFalse(video_output.all_off(("HDMI-1", "HDMI-2")))

    def test_only_the_lcd_present_is_a_success(self) -> None:
        """1.3: no monitor attached is not an error - there is nothing else to switch off."""
        with xrandr_ready(True), \
             mock.patch.object(video_output, "read_outputs",
                               side_effect=[{"HDMI-1": True}, {"HDMI-1": False}]), \
             mock.patch("subprocess.run") as run:
            self.assertTrue(video_output.all_off(("HDMI-1", "HDMI-2")))

        self.assertEqual(run.call_args.args[0], ["xrandr", "--output", "HDMI-1", "--off"])

    def test_an_unexpected_active_output_is_switched_off_too(self) -> None:
        """"Screens off" means nothing lit, not just the two panels we named."""
        with xrandr_ready(True), \
             mock.patch.object(video_output, "read_outputs",
                               side_effect=[{"HDMI-1": True, "Composite-1": True},
                                            {"HDMI-1": False, "Composite-1": False}]), \
             mock.patch("subprocess.run") as run:
            self.assertTrue(video_output.all_off(("HDMI-1", "HDMI-2")))

        self.assertIn("Composite-1", run.call_args.args[0])

    def test_panels_already_off_skip_xrandr(self) -> None:
        """A front rebuilt during the blackout (RF-09) must not re-run xrandr."""
        with xrandr_ready(True), \
             mock.patch.object(video_output, "read_outputs",
                               return_value={"HDMI-1": False, "HDMI-2": False}), \
             mock.patch("subprocess.run") as run:
            self.assertTrue(video_output.all_off(("HDMI-1", "HDMI-2")))

        run.assert_not_called()

    def test_no_display_returns_false_logs_and_does_not_raise(self) -> None:
        """1.4: the developer machine - the command is logged, nothing breaks."""
        with mock.patch.dict("os.environ", {}, clear=True), \
             mock.patch("subprocess.run") as run, \
             self.assertLogs(video_output.logger, level="WARNING") as logs:
            self.assertFalse(video_output.all_off(("HDMI-1", "HDMI-2")))

        run.assert_not_called()
        self.assertIn("WRN-013", "\n".join(logs.output))

    def test_an_x_server_without_xrandr_returns_false(self) -> None:
        with mock.patch.dict("os.environ", {"DISPLAY": ":0"}), \
             mock.patch("shutil.which", return_value=None), \
             mock.patch("subprocess.run") as run, \
             self.assertLogs(video_output.logger, level="WARNING"):
            self.assertFalse(video_output.all_off(("HDMI-1", "HDMI-2")))

        run.assert_not_called()


# Tudo desligado: o ecra X cai para o minimo, mas cada saida conectada continua a
# listar os seus modos - e' dai que o front tira o tamanho durante o blackout.
QUERY_ALL_OFF = """Screen 0: minimum 320 x 200, current 320 x 200, maximum 16384 x 16384
HDMI-1 connected (normal left inverted right x axis y axis) 154mm x 86mm
   800x480       59.90 +
HDMI-2 connected (normal left inverted right x axis y axis) 598mm x 336mm
   1280x720      60.00
   1920x1080     60.00 +  50.00    59.94
"""


class PreferredSizeTest(unittest.TestCase):
    """video-blackout 5.1: sizing for the panel that will relight, not the dark screen."""

    def preferred(self, output: str, stdout: str = QUERY_ALL_OFF):
        with xrandr_ready(True), \
             mock.patch("subprocess.run", return_value=fake_query(stdout)):
            return video_output.preferred_size(output)

    def test_reads_the_mode_marked_preferred(self) -> None:
        self.assertEqual(self.preferred("HDMI-2"), (1920, 1080))

    def test_each_output_has_its_own_preferred_mode(self) -> None:
        self.assertEqual(self.preferred("HDMI-1"), (800, 480))

    def test_without_a_preferred_mark_the_first_mode_is_used(self) -> None:
        stdout = "Screen 0: current 320 x 200\nHDMI-2 connected\n   1280x720      60.00\n"
        self.assertEqual(self.preferred("HDMI-2", stdout), (1280, 720))

    def test_an_output_x_does_not_list_is_unknown(self) -> None:
        self.assertIsNone(self.preferred("DP-1"))

    def test_no_x_is_unknown(self) -> None:
        with xrandr_ready(False):
            self.assertIsNone(video_output.preferred_size("HDMI-2"))

    def test_a_failing_xrandr_is_unknown_not_an_exception(self) -> None:
        with xrandr_ready(True), \
             mock.patch("subprocess.run", side_effect=subprocess.CalledProcessError(1, "xrandr")):
            self.assertIsNone(video_output.preferred_size("HDMI-2"))


# O LCD ligado e virado 180 graus: e' assim que o xrandr reporta o painel depois
# de activate(). A palavra da rotacao vem DEPOIS da geometria e ANTES dos
# parenteses - que listam as rotacoes suportadas e aparecem iguais em toda a
# saida, rodada ou nao.
QUERY_LCD_INVERTED = """Screen 0: minimum 320 x 200, current 800 x 480, maximum 16384 x 16384
HDMI-1 connected primary 800x480+0+0 inverted (normal left inverted right x axis y axis) 154mm x 86mm
   800x480       59.90*+
HDMI-2 connected (normal left inverted right x axis y axis) 598mm x 336mm
   1920x1080     60.00 +  50.00
"""


class ReadRotationsTest(unittest.TestCase):
    """O LCD e' montado de cabeca para baixo: a orientacao tem de ser legivel."""

    def read(self, stdout: str) -> dict[str, str]:
        with xrandr_ready(True, rotations=None), \
             mock.patch("subprocess.run", return_value=fake_query(stdout)):
            return video_output.read_rotations()

    def test_reads_the_rotation_word_printed_after_the_geometry(self) -> None:
        self.assertEqual(
            self.read(QUERY_LCD_INVERTED), {"HDMI-1": "inverted", "HDMI-2": "normal"}
        )

    def test_an_unrotated_output_reads_as_normal(self) -> None:
        """O xrandr nao imprime nada para "normal" - a ausencia e' a resposta."""
        self.assertEqual(self.read(QUERY_LCD_ONLY), {"HDMI-1": "normal", "HDMI-2": "normal"})

    def test_the_supported_rotations_in_parentheses_are_not_the_current_one(self) -> None:
        """"(normal left inverted right ...)" aparece em TODA a saida."""
        self.assertEqual(self.read(QUERY_EXTENDED)["HDMI-1"], "normal")

    def test_an_unreadable_state_is_an_empty_dict(self) -> None:
        with xrandr_ready(False, rotations=None):
            self.assertEqual(video_output.read_rotations(), {})

    def test_a_failing_xrandr_is_unknown_not_an_exception(self) -> None:
        with xrandr_ready(True, rotations=None), \
             mock.patch("subprocess.run", side_effect=subprocess.CalledProcessError(1, "xrandr")):
            self.assertEqual(video_output.read_rotations(), {})

    def test_the_active_state_survives_the_shared_parse(self) -> None:
        """Rotacao e estado saem da mesma linha; ler uma nao pode perder a outra."""
        with xrandr_ready(True, rotations=None), \
             mock.patch("subprocess.run", return_value=fake_query(QUERY_LCD_INVERTED)):
            self.assertEqual(video_output.read_outputs(), {"HDMI-1": True, "HDMI-2": False})


class RotationResolutionTest(unittest.TestCase):
    """Que volta cada painel leva, e como o bring-up a corrige sem recompilar."""

    def rotation(self, env: dict[str, str], env_var: str, default: str) -> str:
        with mock.patch.dict("os.environ", env, clear=True):
            return video_output.rotation(env_var, default)

    def test_the_lcd_is_inverted_by_default(self) -> None:
        """O painel esta' montado de pernas para o ar dentro do gabinete."""
        self.assertEqual(video_output.DEFAULT_LCD_ROTATION, "inverted")
        self.assertEqual(
            self.rotation({}, video_output.LCD_ROTATION_ENV, video_output.DEFAULT_LCD_ROTATION),
            "inverted",
        )

    def test_the_monitor_stays_upright_by_default(self) -> None:
        self.assertEqual(
            self.rotation(
                {}, video_output.MONITOR_ROTATION_ENV, video_output.DEFAULT_MONITOR_ROTATION
            ),
            "normal",
        )

    def test_an_env_var_overrides_the_default(self) -> None:
        self.assertEqual(
            self.rotation(
                {"CALC_LCD_ROTATE": "normal"},
                video_output.LCD_ROTATION_ENV,
                video_output.DEFAULT_LCD_ROTATION,
            ),
            "normal",
        )

    def test_degrees_are_accepted_on_the_bench(self) -> None:
        for degrees, expected in (("0", "normal"), ("90", "left"), ("180", "inverted"),
                                  ("270", "right")):
            self.assertEqual(
                self.rotation(
                    {"CALC_LCD_ROTATE": degrees},
                    video_output.LCD_ROTATION_ENV,
                    video_output.DEFAULT_LCD_ROTATION,
                ),
                expected,
            )

    def test_case_and_spaces_do_not_matter(self) -> None:
        self.assertEqual(
            self.rotation(
                {"CALC_LCD_ROTATE": " Inverted "},
                video_output.LCD_ROTATION_ENV,
                video_output.DEFAULT_LCD_ROTATION,
            ),
            "inverted",
        )

    def test_a_typo_falls_back_to_the_default_and_is_logged(self) -> None:
        """Um valor invalido no argv faria o xrandr recusar a chamada inteira."""
        with mock.patch.dict("os.environ", {"CALC_LCD_ROTATE": "180graus"}, clear=True), \
             self.assertLogs(video_output.logger, level="WARNING") as logs:
            value = video_output.rotation(
                video_output.LCD_ROTATION_ENV, video_output.DEFAULT_LCD_ROTATION
            )

        self.assertEqual(value, "inverted")
        self.assertIn("CALC_LCD_ROTATE", "\n".join(logs.output))


class RotationMatchesTest(unittest.TestCase):
    def test_the_wanted_rotation_already_applied_is_a_match(self) -> None:
        self.assertIs(
            video_output.rotation_matches("HDMI-1", "inverted", {"HDMI-1": "inverted"}), True
        )

    def test_another_rotation_is_not_a_match(self) -> None:
        self.assertIs(
            video_output.rotation_matches("HDMI-1", "inverted", {"HDMI-1": "normal"}), False
        )

    def test_an_unreadable_state_is_neither(self) -> None:
        self.assertIsNone(video_output.rotation_matches("HDMI-1", "inverted", {}))

    def test_an_output_x_does_not_know_is_unreadable(self) -> None:
        self.assertIsNone(
            video_output.rotation_matches("HDMI-9", "inverted", {"HDMI-1": "normal"})
        )


class ActivateRotationTest(unittest.TestCase):
    """A imagem do LCD tem de sair virada 180 graus - e so' a do LCD."""

    def test_the_rotation_travels_in_the_same_xrandr_call(self) -> None:
        """Uma unica reconfiguracao: acender e virar nao sao dois passos."""
        with xrandr_ready(True, rotations={"HDMI-1": "inverted", "HDMI-2": "normal"}), \
             mock.patch.object(video_output, "layout_matches", side_effect=[False, True]), \
             mock.patch("subprocess.run") as run:
            self.assertTrue(
                video_output.activate(
                    "HDMI-1", disable=("HDMI-1", "HDMI-2"), rotate="inverted"
                )
            )

        argv = run.call_args.args[0]
        self.assertEqual(
            argv[:7],
            ["xrandr", "--output", "HDMI-1", "--auto", "--primary", "--rotate", "inverted"],
        )
        run.assert_called_once()

    def test_a_panel_lit_but_upside_down_is_reconfigured(self) -> None:
        """O layout ja' esta' certo e mesmo assim ha' trabalho a fazer."""
        with xrandr_ready(True, rotations={"HDMI-1": "normal"}), \
             mock.patch.object(video_output, "read_outputs",
                               return_value={"HDMI-1": True, "HDMI-2": False}), \
             mock.patch("subprocess.run") as run:
            video_output.activate("HDMI-1", disable=("HDMI-2",), rotate="inverted")

        run.assert_called_once()

    def test_the_right_layout_in_the_right_rotation_skips_xrandr(self) -> None:
        with xrandr_ready(True, rotations={"HDMI-1": "inverted"}), \
             mock.patch.object(video_output, "read_outputs",
                               return_value={"HDMI-1": True, "HDMI-2": False}), \
             mock.patch("subprocess.run") as run:
            self.assertTrue(
                video_output.activate("HDMI-1", disable=("HDMI-2",), rotate="inverted")
            )

        run.assert_not_called()

    def test_xrandr_succeeding_while_the_image_stays_upright_is_a_failure(self) -> None:
        """Mesmo argumento do CRTC: o codigo de saida nao prova a rotacao."""
        with xrandr_ready(True, rotations={"HDMI-1": "normal"}), \
             mock.patch.object(video_output, "layout_matches", side_effect=[False, True]), \
             mock.patch("subprocess.run"), \
             self.assertLogs(video_output.logger, level="WARNING") as logs:
            self.assertFalse(
                video_output.activate(
                    "HDMI-1", disable=("HDMI-2",), mode="lcd", rotate="inverted"
                )
            )

        recorded = "\n".join(logs.output)
        self.assertIn("WRN-012", recorded)
        self.assertIn("inverted", recorded)

    def test_an_unverifiable_rotation_is_reported_but_does_not_raise(self) -> None:
        with xrandr_ready(True, rotations={}), \
             mock.patch.object(video_output, "layout_matches", side_effect=[False, True]), \
             mock.patch("subprocess.run"), \
             self.assertLogs(video_output.logger, level="WARNING"):
            self.assertFalse(
                video_output.activate("HDMI-1", disable=("HDMI-2",), rotate="inverted")
            )

    def test_an_unknown_rotation_never_reaches_the_argv(self) -> None:
        """O xrandr recusaria a chamada inteira e o painel ficaria apagado."""
        with xrandr_ready(True), \
             mock.patch.object(video_output, "layout_matches", side_effect=[False, True]), \
             mock.patch("subprocess.run") as run, \
             self.assertLogs(video_output.logger, level="WARNING"):
            self.assertTrue(
                video_output.activate("HDMI-2", disable=("HDMI-1",), rotate="de-lado")
            )

        self.assertNotIn("de-lado", run.call_args.args[0])
        self.assertIn("normal", run.call_args.args[0])
