GustaEagle/TCC_Calculadora_Acessivel/software/ui/hdmi/app.py

"""ttkbootstrap front-end for the external HDMI monitor.

Sibling of ui/lcd/app.py, not an extension of it: the monitor gets its own
composition (persistent history panel beside the keypad, PRD §8 "maior area,
layout mais rico") instead of the 800x480 panel arrangement.

Non-resizable window whose layout is derived once, at construction, from the
active display - there is no resize path to get wrong. Both the size and the
composition come from the real resolution rather than a fixed reference: the
kiosk has no window manager, so X places the window at (0,0) and a 1280x720
window on a 1920x1080 monitor would sit in a corner.

What the resolution decides is in ui/shared/layout.py: the typographic scale
and which panels fit. On a small monitor the keypad and the history panel are
not built at all (the physical keyboard stays the real input, RF-05), the same
way the Windows calculator drops panels as it narrows.
"""

from __future__ import annotations

import logging
import os

try:
    import ttkbootstrap as ttk
    from ttkbootstrap.constants import BOTH, E, EW, LEFT, NSEW, RIGHT, W, X
except ImportError as exc:  # pragma: no cover - user-facing startup guard
    raise SystemExit(
        "Instale as dependencias com: python -m pip install -r software/requirements.txt"
    ) from exc

from software.accessibility.speech import SpeechService
from software.core import CalculatorState
from software.hw_platform.display import (
    DEFAULT_MONITOR_CONNECTOR,
    MONITOR_CONNECTOR_ENV,
    DisplayMode,
)
from software.hw_platform.keyboard import KeyboardAdapter
from software.hw_platform.keypad_matrix import KeyEvent, MatrixKeyboard
from software.hw_platform import video_output
from software.ui.shared.error_messages import friendly_message, spoken_priority_prefix
from software.ui.shared.formatting import FUNCTION_DISPLAY_SYMBOLS, format_expression_for_display
from software.ui.shared.history import recent_entries, spoken_history
from software.ui.shared.layout import (
    LayoutTier,
    display_limits,
    font_sizes,
    scale_for,
    tier_for,
)
from software.ui.shared.keypad import (
    HISTORY_TOKEN,
    LEFT_BUTTONS,
    NO_FUNCTION_SPEECH,
    RIGHT_BUTTONS,
    button_style,
    keypad_toggle_label,
    keypad_toggle_speech,
    spoken_token,
)
from software.ui.shared.palette import BUTTON_PALETTE, DISPLAY_BACKGROUND, DISPLAY_FOREGROUND
from software.ui.shared.tk_session import reset_ttkbootstrap_globals
from software.ui.shared.video_blackout import (
    BLACKOUT_TOKEN,
    VideoApplier,
    VideoBlackout,
    no_video_control,
    relight_on_ac,
    toggle,
)
from software.ui.shared.matrix_input import MatrixInputPump
from software.ui.shared.video_watch import VideoOutputWatch

logger = logging.getLogger(__name__)

# Resolução de referência do layout. A janela adota o tamanho da tela ativa
# (ver screen_geometry); estes valores permanecem como recurso final para um Tk
# que não consiga informar um tamanho de tela utilizável.
WINDOW_WIDTH = 1280
WINDOW_HEIGHT = 720


def screen_geometry(width: int, height: int) -> str:
    """Tk geometry string for a screen of `width`x`height`.

    A screen size Tk cannot report sensibly falls back to the reference
    resolution: a zero-sized window would hide the calculator entirely, which
    is worse than a window that does not fill the panel.
    """
    if width < 1 or height < 1:
        return f"{WINDOW_WIDTH}x{WINDOW_HEIGHT}"
    return f"{width}x{height}"

# Tipografia e truncamento saem de ui/shared/layout.py, derivados da resolucao
# ativa na construcao (self.fonts / self.max_expression_chars). A tabela-base
# de 1280x720 vive la como BASE_FONT_SIZES, para escala 1.0 reproduzir
# exatamente a aparencia que este front tinha quando era de tamanho fixo.

_HISTORY_VISIBLE_ROWS = 10


class CalculatorApp:
    """Visual shell for the external monitor, sized from the active display."""

    def __init__(
        self,
        state: CalculatorState | None = None,
        speech: SpeechService | None = None,
        blackout: VideoBlackout | None = None,
        apply_video: VideoApplier | None = None,
        keypad_matrix: MatrixKeyboard | None = None,
    ) -> None:
        # Injected when the other front hands over (RF-09): reusing the same
        # state keeps the expression, history and angle mode across the swap,
        # and reusing the SpeechService avoids restarting the TTS worker.
        self.state = state or CalculatorState()
        self.speech = speech or SpeechService()
        self.keyboard = KeyboardAdapter()
        # The blackout travels the same way, so a front built during it is born
        # dark; apply_video is the entry point's single place that touches X.
        self.blackout = blackout or VideoBlackout()
        self.apply_video = apply_video or no_video_control

        # RF-09: this may be the SECOND window this process builds. ttkbootstrap
        # keeps its Style in a class-level singleton bound to the previous
        # (destroyed) interpreter, and would hand it back unbuilt - the window
        # would come up in Tk's default theme with none of the palette.
        reset_ttkbootstrap_globals()

        self.root = ttk.Window(themename="darkly")
        self.root.title("Calculadora Cientifica Acessivel")

        # Tela ativa lida UMA vez: alimenta tanto o tamanho da janela quanto a
        # composicao do layout, e evita um segundo `xrandr --query` no arranque.
        # Sem gerenciador de janelas o X coloca a janela em (0,0), entao ela
        # precisa cobrir o painel inteiro. Numa troca de saida (RF-09) o front e'
        # RECONSTRUIDO e a tela nova e' lida aqui de novo - nada disto vira
        # estado de modulo.
        self.screen_width, self.screen_height = self._active_screen_size()
        self.screen_width = max(1, self.screen_width)
        self.screen_height = max(1, self.screen_height)

        self.root.geometry(screen_geometry(self.screen_width, self.screen_height))
        self.root.resizable(False, False)

        screen_width, screen_height = self.screen_width, self.screen_height
        self.tier = tier_for(screen_width, screen_height)
        self.scale = scale_for(screen_width, screen_height)
        self.fonts = font_sizes(self.scale)
        self.max_expression_chars, self.max_result_chars = display_limits(
            screen_width, self.scale
        )
        logger.info(
            "Layout HDMI: %sx%s (tk dizia %sx%s) -> faixa %s, escala %.2f",
            screen_width, screen_height,
            self.root.winfo_screenwidth(), self.root.winfo_screenheight(),
            self.tier.value, self.scale,
        )

        self.style = ttk.Style()

        self.ctrl_active = False
        self.shift_active = False
        # Widgets que so existem na sua faixa de layout (ver ui/shared/layout.py):
        # ficam None nas faixas menores, e os metodos abaixo tratam esse caso.
        self.buttons: dict[str, ttk.Button] = {}
        self.keypad_frame: ttk.Frame | None = None
        self.toggle_btn: ttk.Button | None = None
        self.history_frame: ttk.Frame | None = None

        self.expression_var = ttk.StringVar(value="")
        self.result_var = ttk.StringVar(value="Pronto")

        self.mode_var = ttk.StringVar(value="DEG")
        self.ctrl_var = ttk.StringVar(value="")
        self.shift_var = ttk.StringVar(value="")
        # Teclado na tela começa VISÍVEL onde couber (faixas média/completa):
        # a entrada real é o teclado físico (RF-05), mas mostrar as teclas ajuda
        # quem enxerga parcialmente a localizar a operação. O botão do rodapé
        # oculta a qualquer momento; na faixa compacta nem chega a ser montado.
        self.controls_visible = True

        self.expression_disp_var = ttk.StringVar(value="")
        self.result_disp_var = ttk.StringVar(value="")

        self._configure_styles()
        self._configure_palette()
        self._build_layout()
        self._apply_controls_visibility()
        self._bind_keyboard()
        self._set_initial_focus()

        # RF-09: unplugging the monitor has to hand the UI back to the LCD.
        self.video_watch = VideoOutputWatch(self.root, self.speech, DisplayMode.HDMI)

        # RF-05: the physical keypad. The scanner belongs to the entry point
        # (one GPIO request per run, kept across front swaps); this front only
        # plugs its token handler in while its window exists.
        self.matrix_input: MatrixInputPump | None = None
        if keypad_matrix is not None:
            self.matrix_input = MatrixInputPump(
                self.root, keypad_matrix,
                on_press=self._handle_token, on_unmapped=self._on_unmapped_key,
            )

        self.expression_var.trace_add("write", lambda *_: self._update_display())
        self.result_var.trace_add("write", lambda *_: self._update_display())

    def _active_screen_size(self) -> tuple[int, int]:
        """Real size of the panel this front is about to fill.

        xrandr first, Tk second. winfo_screenwidth()/winfo_screenheight() read
        Xlib's `Screen` struct, which is filled when the display connection
        opens and is NOT refreshed when RandR resizes the screen - and the case
        that matters is exactly that one: the monitor is always plugged in with
        the calculator already running (RF-09), so this front is built moments
        after xrandr switched panels, when Tk would still report the LCD's
        800x480. Sizing from that stale value put the window - and the layout
        tier - on the wrong panel.

        Off the Pi (no X, no xrandr) screen_size() returns None and Tk's value
        is both available and correct, since nothing resized anything.

        During a blackout (a hotplug rebuilt this front with every CRTC off)
        the X screen is whatever is left with no active output, so the size
        comes from the monitor's preferred mode instead - the panel that will
        relight - and only an unreadable answer falls back to the paths above.
        """
        if self.blackout.active:
            monitor = video_output.output_name(
                os.environ.get(MONITOR_CONNECTOR_ENV, DEFAULT_MONITOR_CONNECTOR),
                video_output.MONITOR_OUTPUT_ENV,
            )
            preferred = video_output.preferred_size(monitor)
            if preferred is not None:
                return preferred

        from_xrandr = video_output.screen_size()
        if from_xrandr is not None:
            return from_xrandr
        return self.root.winfo_screenwidth(), self.root.winfo_screenheight()

    def _screen_geometry(self) -> str:
        """`WxH` da tela ativa, a partir do tamanho ja lido na construcao."""
        return screen_geometry(self.screen_width, self.screen_height)

    def _configure_styles(self) -> None:
        """Fontes fixas: a janela não redimensiona, então isto roda uma só vez."""
        self.style.configure("TLabel", font=("Segoe UI", self.fonts["label"]))
        self.style.configure(
            "Display.TLabel", font=("Segoe UI", self.fonts["expression"]), padding=10,
            foreground=DISPLAY_FOREGROUND, background=DISPLAY_BACKGROUND,
        )
        self.style.configure(
            "Result.TLabel", font=("Segoe UI", self.fonts["result"], "bold"), padding=10,
            foreground=DISPLAY_FOREGROUND, background=DISPLAY_BACKGROUND,
        )
        self.style.configure("Indicator.TLabel", font=("Segoe UI", self.fonts["label"], "bold"))
        self.style.configure("History.TLabel", font=("Segoe UI", self.fonts["history"]))
        self.style.configure("HistoryValue.TLabel", font=("Segoe UI", self.fonts["history"], "bold"))

        self.style.configure("TButton", font=("Segoe UI", self.fonts["button"], "bold"))
        for category in BUTTON_PALETTE:
            self.style.configure(f"{category}.TButton", font=("Segoe UI", self.fonts["button"], "bold"))

    def _configure_palette(self) -> None:
        """Same WCAG-verified palette as the LCD front (ui/shared/palette.py):
        ttkbootstrap's built-in colors are not guaranteed to meet WCAG AA."""
        for category, colors in BUTTON_PALETTE.items():
            self.style.configure(
                f"{category}.TButton",
                background=colors.background,
                foreground=colors.foreground,
            )
            # Pressed/focused states must stay perceivable without relying on
            # color alone: press inverts fg/bg, focus gets a bright border.
            self.style.map(
                f"{category}.TButton",
                background=[("pressed", colors.foreground), ("active", colors.background)],
                foreground=[("pressed", colors.background)],
                bordercolor=[("focus", "#FFFFFF")],
                relief=[("pressed", "sunken")],
            )

    def _update_display(self) -> None:
        """Truncate to what fits the fixed window at the declared font sizes."""
        expr = format_expression_for_display(self.expression_var.get())
        res = self.result_var.get()

        max_expr = self.max_expression_chars
        max_res = self.max_result_chars

        if len(expr) > max_expr:
            self.expression_disp_var.set("..." + expr[-(max_expr - 3):])
        else:
            self.expression_disp_var.set(expr)

        if len(res) > max_res:
            self.result_disp_var.set(".." + res[-(max_res - 2):])
        else:
            self.result_disp_var.set(res)

    # ------------------------------------------------------------------
    # Layout
    # ------------------------------------------------------------------

    def run(self) -> DisplayMode | None:
        """Run until closed.

        Returns the mode that should take over when the video output changed
        under us, or None when the user simply quit.
        """
        self.speech.say("Calculadora pronta. Saida no monitor.")
        self.video_watch.start()
        if self.matrix_input is not None:
            self.matrix_input.start()
        try:
            self.root.mainloop()
        finally:
            if self.matrix_input is not None:
                self.matrix_input.stop()

        if self.video_watch.changed_to is None:
            self.speech.stop()
        return self.video_watch.changed_to

    def _build_layout(self) -> None:
        root_frame = ttk.Frame(self.root, padding=12)
        root_frame.pack(fill=BOTH, expand=True)
        root_frame.columnconfigure(0, weight=1)
        root_frame.rowconfigure(0, weight=0)  # top bar
        root_frame.rowconfigure(1, weight=1)  # main area
        root_frame.rowconfigure(2, weight=0)  # footer

        top_bar = ttk.Frame(root_frame)
        top_bar.grid(row=0, column=0, sticky=EW, pady=(0, 6))
        ttk.Label(top_bar, textvariable=self.mode_var, bootstyle="info", style="Indicator.TLabel").pack(side=LEFT, padx=6)
        ttk.Label(top_bar, textvariable=self.ctrl_var, bootstyle="warning", style="Indicator.TLabel").pack(side=LEFT, padx=6)
        ttk.Label(top_bar, textvariable=self.shift_var, bootstyle="success", style="Indicator.TLabel").pack(side=LEFT, padx=6)

        # Main area: calculator on the left, persistent history on the right.
        # Weights (not pixel widths) are what make this track the window size.
        main = ttk.Frame(root_frame)
        main.grid(row=1, column=0, sticky=NSEW)
        main.rowconfigure(0, weight=1)
        main.columnconfigure(0, weight=3, uniform="main")
        if self.tier.shows_history:
            # So configurada quando o painel existe: uma coluna com peso e sem
            # conteudo reservaria area vazia justamente na tela mais apertada.
            main.columnconfigure(1, weight=1, uniform="main")

        calculator = ttk.Frame(main)
        calculator.grid(
            row=0, column=0, sticky=NSEW,
            padx=(0, 10) if self.tier.shows_history else 0,
        )
        calculator.columnconfigure(0, weight=1)
        if self.tier.shows_keypad:
            calculator.rowconfigure(0, weight=2)  # display
            calculator.rowconfigure(1, weight=5)  # keypad
        else:
            # Sem teclado, o display fica com a altura toda em vez de deixar
            # 5/7 da calculadora em branco.
            calculator.rowconfigure(0, weight=1)

        display = ttk.Frame(calculator, bootstyle="secondary", padding=12)
        display.grid(row=0, column=0, sticky=NSEW, pady=(0, 10))
        display.columnconfigure(0, weight=1)
        display.rowconfigure(0, weight=1)
        display.rowconfigure(1, weight=2)

        self.expression_label = ttk.Label(
            display, textvariable=self.expression_disp_var, anchor=E,
            style="Display.TLabel", bootstyle="inverse-secondary",
        )
        self.expression_label.grid(row=0, column=0, sticky=NSEW)

        self.result_label = ttk.Label(
            display, textvariable=self.result_disp_var, anchor=E,
            style="Result.TLabel", bootstyle="inverse-secondary",
        )
        self.result_label.grid(row=1, column=0, sticky=NSEW)

        # Teclado e historico NAO sao criados fora da sua faixa (em vez de
        # criados e escondidos): um widget escondido continua no grid do pai e
        # mantem o peso da coluna reservado. self.keypad_frame fica None para o
        # resto da classe saber que nao ha teclado nesta execucao.
        if self.tier.shows_keypad:
            self.keypad_frame = ttk.Frame(calculator)
            self.keypad_frame.grid(row=1, column=0, sticky=NSEW)
            self.keypad_frame.rowconfigure(0, weight=1)
            self.keypad_frame.columnconfigure(0, weight=3, uniform="kp")
            self.keypad_frame.columnconfigure(1, weight=4, uniform="kp")

            left_frame = ttk.Frame(self.keypad_frame)
            left_frame.grid(row=0, column=0, sticky=NSEW, padx=(0, 8))
            for i in range(6):
                left_frame.rowconfigure(i, weight=1, uniform="row")
            for i in range(3):
                left_frame.columnconfigure(i, weight=1, uniform="col_left")

            right_frame = ttk.Frame(self.keypad_frame)
            right_frame.grid(row=0, column=1, sticky=NSEW)
            for i in range(6):
                right_frame.rowconfigure(i, weight=1, uniform="row")
            for i in range(4):
                right_frame.columnconfigure(i, weight=1, uniform="col_right")

            self._build_buttons(left_frame, LEFT_BUTTONS, is_left=True)
            self._build_buttons(right_frame, RIGHT_BUTTONS, is_left=False)

        if self.tier.shows_history:
            self._build_history_panel(main)

        # Rodapé só com o botão do teclado: nada de indicar qual saída de video
        # ou fonte de energia está em uso - isso é diagnóstico, não interface.
        # Sem teclado nesta faixa o botao nao e' criado: oferecer uma acao sem
        # efeito e' pior para quem navega por Tab ou ouve os anuncios.
        if self.tier.shows_keypad:
            footer = ttk.Frame(root_frame, padding=(0, 6))
            footer.grid(row=2, column=0, sticky=EW, pady=(8, 0))
            # Discreto de propósito: estilo "link" (sem moldura) e fonte pequena,
            # para não roubar área da tela. Continua focável por Tab e anunciado
            # por voz.
            self.toggle_btn = ttk.Button(
                footer, text=keypad_toggle_label(self.controls_visible),
                bootstyle="secondary-link", command=self._toggle_controls,
            )
            compact = f"Compact.{self.toggle_btn.cget('style')}"
            self.style.configure(compact, font=("Segoe UI", self.fonts["label"]), padding=(6, 2))
            self.toggle_btn.configure(style=compact)
            self.toggle_btn.pack(side=LEFT)

    def _build_buttons(self, container: ttk.Frame, rows: list, is_left: bool) -> None:
        for r, row in enumerate(rows):
            curr_col = 0
            for item in row:
                label, primary, secondary = item[0], item[1], item[2]
                shifted = item[3] if len(item) > 3 else None
                if not label:
                    curr_col += 1
                    continue

                btn_id = f"{primary}_{secondary}"
                button = ttk.Button(
                    container, text=label, bootstyle=button_style(primary),
                    command=lambda p=primary, s=secondary, sh=shifted: self._handle_token(p, s, sh),
                )

                cspan = 1
                if is_left:
                    if (r == 3 and primary == "inv(") or (r == 5 and primary == "Ctrl"):
                        cspan = 2
                elif r == 4 and primary == "0":
                    cspan = 2

                button.grid(row=r, column=curr_col, sticky=NSEW, padx=4, pady=4, columnspan=cspan)
                self.buttons[btn_id] = button
                curr_col += cspan

    def _build_history_panel(self, parent: ttk.Frame) -> None:
        """The extra area the monitor has over the LCD: history always visible
        instead of behind a dialog."""
        panel = ttk.Frame(parent, bootstyle="secondary", padding=10)
        panel.grid(row=0, column=1, sticky=NSEW)
        panel.columnconfigure(0, weight=1)
        panel.rowconfigure(1, weight=1)

        ttk.Label(
            panel, text="Historico", anchor=W, style="Indicator.TLabel",
            bootstyle="inverse-secondary",
        ).grid(row=0, column=0, sticky=EW, pady=(0, 8))

        self.history_frame = ttk.Frame(panel)
        self.history_frame.grid(row=1, column=0, sticky=NSEW)
        self.history_frame.columnconfigure(0, weight=1)

        self._refresh_history()

    def _refresh_history(self) -> None:
        # Faixas menores nao montam o painel; o historico continua no
        # CalculatorState (e e' anunciado por voz), so nao tem onde ser pintado.
        if self.history_frame is None:
            return
        for child in self.history_frame.winfo_children():
            child.destroy()

        recent = recent_entries(self.state.history, _HISTORY_VISIBLE_ROWS)
        if not recent:
            ttk.Label(
                self.history_frame, text="Nenhuma operacao ainda.",
                anchor=W, style="History.TLabel",
            ).grid(row=0, column=0, sticky=EW)
            return

        for index, result in enumerate(recent):
            row = ttk.Frame(self.history_frame)
            row.grid(row=index, column=0, sticky=EW, pady=2)
            row.columnconfigure(0, weight=1)
            ttk.Label(
                row, text=format_expression_for_display(result.expression),
                anchor=W, style="History.TLabel",
            ).grid(row=0, column=0, sticky=EW)
            ttk.Label(
                row, text=f"= {result.display}", anchor=E, style="HistoryValue.TLabel",
            ).grid(row=1, column=0, sticky=EW)

    def _apply_controls_visibility(self) -> None:
        """Sincroniza teclado e rótulo do botão com self.controls_visible.

        Na faixa compacta nao ha teclado nem botao para sincronizar: a escolha
        do usuario so existe onde o teclado cabe.
        """
        if self.keypad_frame is None:
            return
        if self.controls_visible:
            self.keypad_frame.grid()
        else:
            self.keypad_frame.grid_remove()
        if self.toggle_btn is not None:
            self.toggle_btn.configure(text=keypad_toggle_label(self.controls_visible))

    def _set_initial_focus(self) -> None:
        """Give Tab traversal a predictable starting point.

        Com o teclado visível, começa no primeiro dígito. Se o usuário o
        ocultou, o ponto de partida passa a ser o botão que o revela - senão o
        Tab começaria em algo invisível. E na faixa compacta, onde nem teclado
        nem botão existem, sobra a própria janela (a entrada é física, RF-05).
        """
        if self.controls_visible:
            first_digit = self.buttons.get("7_None")
            if first_digit is not None:
                first_digit.focus_set()
                return
        if self.toggle_btn is not None:
            self.toggle_btn.focus_set()
            return
        # Faixa compacta: nao ha widget focavel na tela. A janela recebe o foco
        # para que as teclas fisicas (RF-05, a entrada real) continuem chegando.
        self.root.focus_set()

    def _toggle_controls(self) -> None:
        self.controls_visible = not self.controls_visible
        self._apply_controls_visibility()
        self.speech.say(keypad_toggle_speech(self.controls_visible))

    # ------------------------------------------------------------------
    # Input handling (mirrors ui/lcd so both fronts behave identically)
    # ------------------------------------------------------------------

    def _bind_keyboard(self) -> None:
        self.root.bind("<Key>", self._on_key)
        self.root.bind("<Return>", lambda _event: self._handle_token("=", None, None))
        self.root.bind("<BackSpace>", lambda _event: self._handle_token("DEL", None, None))
        self.root.bind("<Escape>", lambda _event: self._handle_token("AC", None, None))
        self.root.bind("<Control_L>", lambda _event: self._handle_token("Ctrl", None, None))
        self.root.bind("<Control_R>", lambda _event: self._handle_token("Ctrl", None, None))
        self.root.bind("<Shift_L>", lambda _event: self._handle_token("Shift", None, None))
        self.root.bind("<Shift_R>", lambda _event: self._handle_token("Shift", None, None))

    def _on_key(self, event: object) -> None:
        char = getattr(event, "char", "")
        token = self.keyboard.map_key(char)
        if token:
            logger.debug("key event: char=%r -> token=%r", char, token)
            self._handle_token(token, None, None)

    def _on_unmapped_key(self, event: KeyEvent) -> None:
        # A "?" da matriz: lida, mas sem função no catálogo. Sem este anúncio,
        # quem não vê a tela acharia que a tecla está avariada.
        logger.info("tecla sem função: %s %s %r", event.switch, event.coord, event.keycap)
        self.speech.say(NO_FUNCTION_SPEECH)

    def _handle_token(self, primary: str, secondary: str | None, shifted: str | None = None) -> None:
        # Vindo do teclado (_on_key) não há 'secondary'; sem isto o Ctrl + Ans
        # do teclado físico não abriria o histórico - só o clique no botão.
        if primary == "Ans" and secondary is None:
            secondary = HISTORY_TOKEN
        # Idem para o AC: Ctrl + AC (Ctrl e depois Esc no PC) apaga/religa as telas.
        if primary == "AC" and secondary is None:
            secondary = BLACKOUT_TOKEN

        if self.ctrl_active and self.shift_active and primary not in {"Ctrl", "Shift"}:
            main_name = spoken_token(primary)
            ctrl_name = spoken_token(secondary) if secondary else "Nenhuma"
            shift_name = spoken_token(shifted) if shifted else "Nenhuma"

            msg = f"Função {main_name}."
            msg += f" Com Controle ativo, função {ctrl_name}."
            msg += f" Com Shift ativo, função {shift_name}."
            self.speech.say(msg)
            return

        if primary == "Ctrl":
            self.ctrl_active = not self.ctrl_active
            self.ctrl_var.set("CTRL" if self.ctrl_active else "")
            self._update_keypad_labels()
            self.speech.say("Controle ativo" if self.ctrl_active else "Controle desativado")
            return

        if primary == "Shift":
            self.shift_active = not self.shift_active
            self.shift_var.set("SHIFT" if self.shift_active else "")
            self._update_keypad_labels()
            self.speech.say("Shift ativo" if self.shift_active else "Shift desativado")
            return

        token = primary
        if self.shift_active and shifted:
            token = shifted
            self.shift_active = False
            self.shift_var.set("")
            self._update_keypad_labels()
        elif self.ctrl_active and secondary:
            token = secondary
            self.ctrl_active = False
            self.ctrl_var.set("")
            self._update_keypad_labels()

        # Depois dos modificadores: na matriz e na tela o RAD/DEG é o Shift + /.
        if token == "RAD/DEG":
            self.state.press("RAD/DEG")
            self.mode_var.set(self.state.angle_mode.upper())
            self.speech.say(f"Modo {self.state.angle_mode}")
            return

        # Função secundária: substitui o AC (não limpa a expressão) e já
        # consumiu o Ctrl acima, como qualquer outra.
        if token == BLACKOUT_TOKEN:
            self.speech.interrupt_and_say(toggle(self.blackout, self.apply_video))
            return

        # AC sozinho sempre religa uma tela apagada - a saída para quem apagou
        # por engano - e depois segue limpando a expressão como sempre.
        if token == "AC":
            relit = relight_on_ac(self.blackout, self.apply_video)
            if relit is not None:
                self.speech.interrupt_and_say(relit)

        if token == "RECALL":
            self._recall_last_answer()
            return

        if token == HISTORY_TOKEN:
            self._announce_history()
            return

        if token == "=" and not self.state.expression:
            return

        is_digit_or_func = token.isdigit() or token == "Ans" or "(" in token or token in {"π", "e"}
        if self.state.last_result and self.state.last_result.ok and is_digit_or_func:
            self.state.press("AC")

        operators = {"+", "-", "*", "/", "^"}

        # Chaining: after a result, an operator continues from Ans.
        if self.state.last_result and self.state.last_result.ok and token in operators:
            self.state.expression = "Ans"
            self.state.last_result = None

        if token in operators and self.state.expression:
            if self.state.expression[-1] in operators:
                self.speech.say("Substituindo")
                self.state.press("DEL")

        result = self.state.press(token)
        self.expression_var.set(self.state.expression)

        if result is None:
            self.speech.say(spoken_token(token))
            return

        if result.ok:
            self.result_var.set(result.display)
            self.speech.interrupt_and_say(f"Resultado {result.display}")
        else:
            # Same friendly text on screen and in speech, with the PRD §13
            # priority prefix (P1 -> "Erro", P2 -> "Aviso").
            friendly_msg = friendly_message(result.code, result.message)
            prefix = spoken_priority_prefix(result.code)
            self.result_var.set(f"{result.code}: {friendly_msg}")
            self.speech.interrupt_and_say(f"{prefix} {result.code.split('-')[-1]}. {friendly_msg}")

        self._refresh_history()

    def _update_keypad_labels(self) -> None:
        symbol_labels = {token: symbol.rstrip("(") for token, symbol in FUNCTION_DISPLAY_SYMBOLS.items()}
        ctrl_map = {
            **symbol_labels, "ln(": "ln", "nPr(": "nPr", "e": "e",
            "RECALL": "Últ. resp.", HISTORY_TOKEN: "Histórico", BLACKOUT_TOKEN: "Telas",
        }
        shift_map = {
            "logbase(": symbol_labels["logbase("], ",": ",",
            "RAD/DEG": "Deg/Rad", "RECALL": "Últ. resp.",
        }

        for row in LEFT_BUTTONS + RIGHT_BUTTONS:
            for item in row:
                label, primary, secondary = item[0], item[1], item[2]
                shifted = item[3] if len(item) > 3 else None
                if not label:
                    continue

                button = self.buttons.get(f"{primary}_{secondary}")
                if button is None:
                    continue

                new_text = label
                new_style = button_style(primary)
                if self.shift_active and shifted:
                    new_text = shift_map.get(shifted, shifted.rstrip("("))
                    new_style = "info"
                elif self.ctrl_active and secondary:
                    new_text = ctrl_map.get(secondary, secondary.rstrip("("))
                    new_style = "info"

                button.configure(text=new_text, bootstyle=new_style)

    def _recall_last_answer(self) -> None:
        """Re-announce/redisplay the last full result without recalculating."""
        result = self.state.recall_last_answer()
        if result.ok:
            self.result_var.set(result.display)
            self.speech.interrupt_and_say(f"Última resposta: {result.display}")
        else:
            friendly_msg = friendly_message(result.code, result.message)
            prefix = spoken_priority_prefix(result.code)
            self.speech.interrupt_and_say(f"{prefix} {result.code.split('-')[-1]}. {friendly_msg}")

    def _announce_history(self) -> None:
        """Ctrl + Ans: o painel já está visível aqui, então basta anunciar.

        Mantém o histórico acessível por voz (RF-04/RF-07) sem depender de
        enxergar o painel.
        """
        self._refresh_history()
        entries = recent_entries(self.state.history, _HISTORY_VISIBLE_ROWS)
        self.speech.interrupt_and_say(spoken_history(entries))


def main() -> None:
    CalculatorApp().run()


if __name__ == "__main__":
    main()
